AzizSfar/modular_shadow_lamp/output/analytic_projection.png

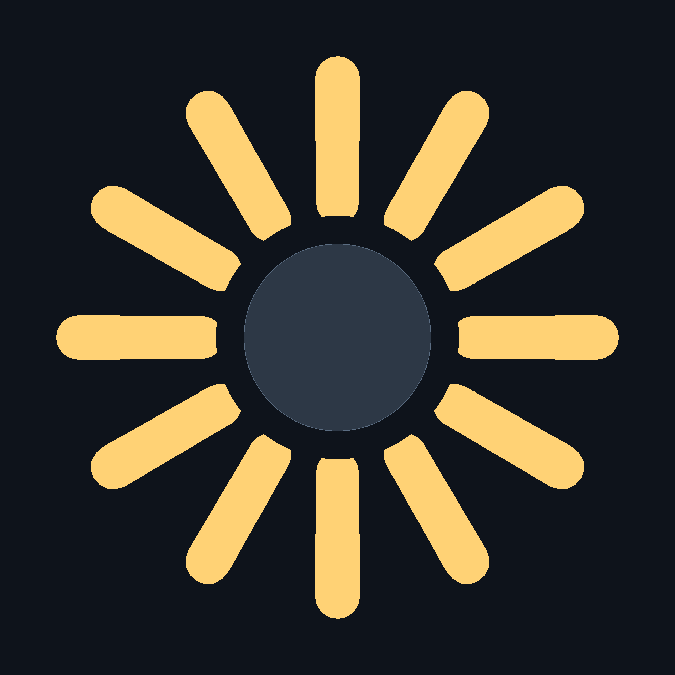
output/analytic_projection.png
