AzizSfar/modular_shadow_lamp/output/demo_projection.png

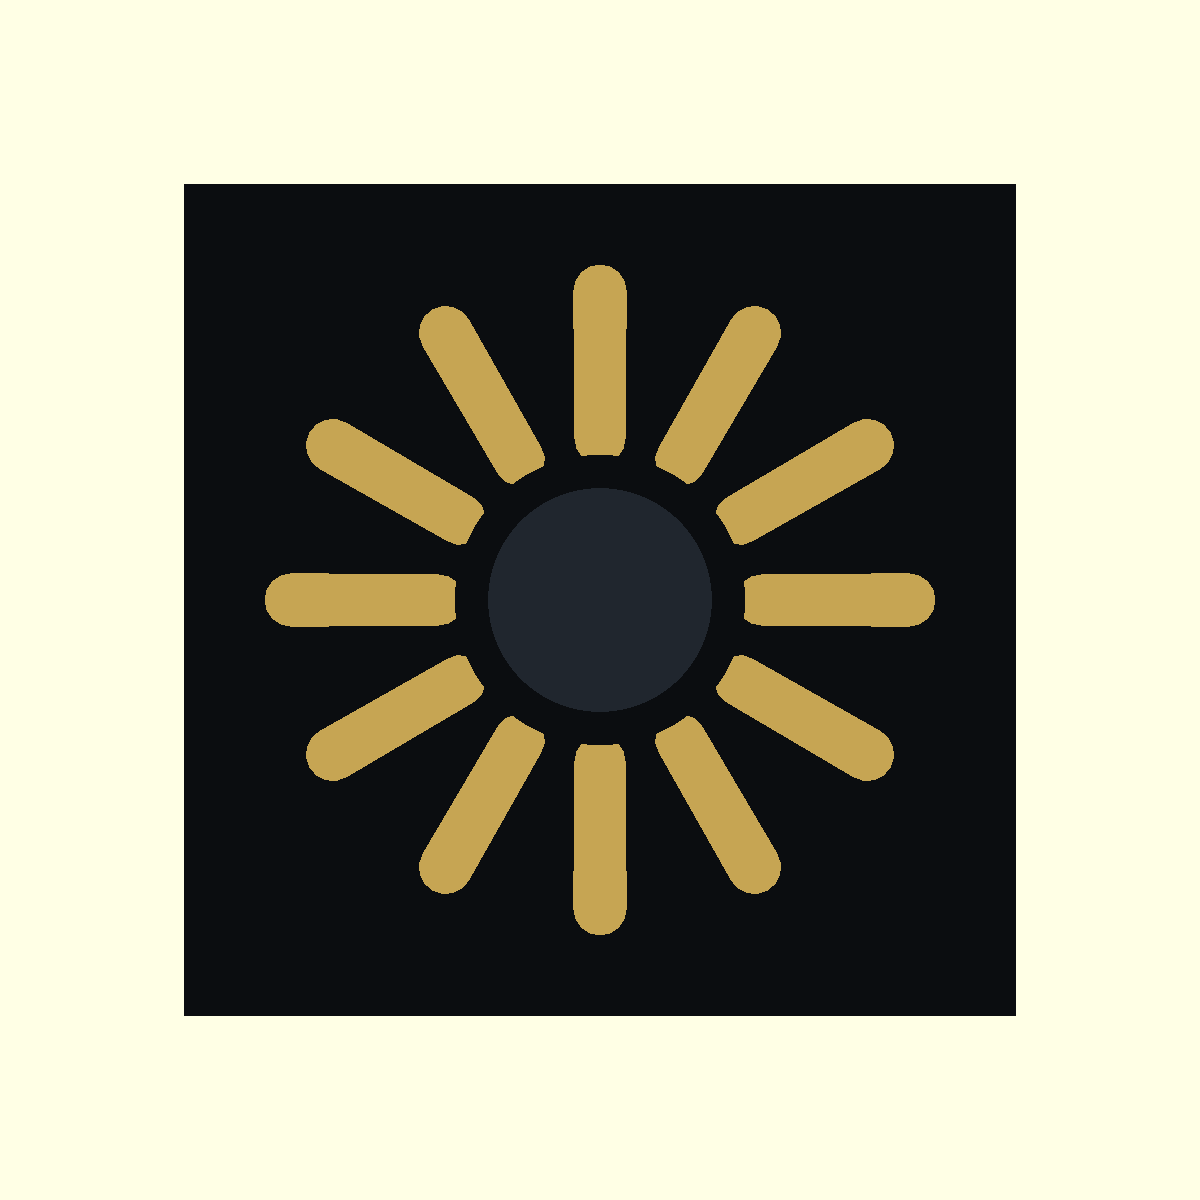
output/demo_projection.png
