AzizSfar/modular_shadow_lamp/output/features_analytic_projection.png

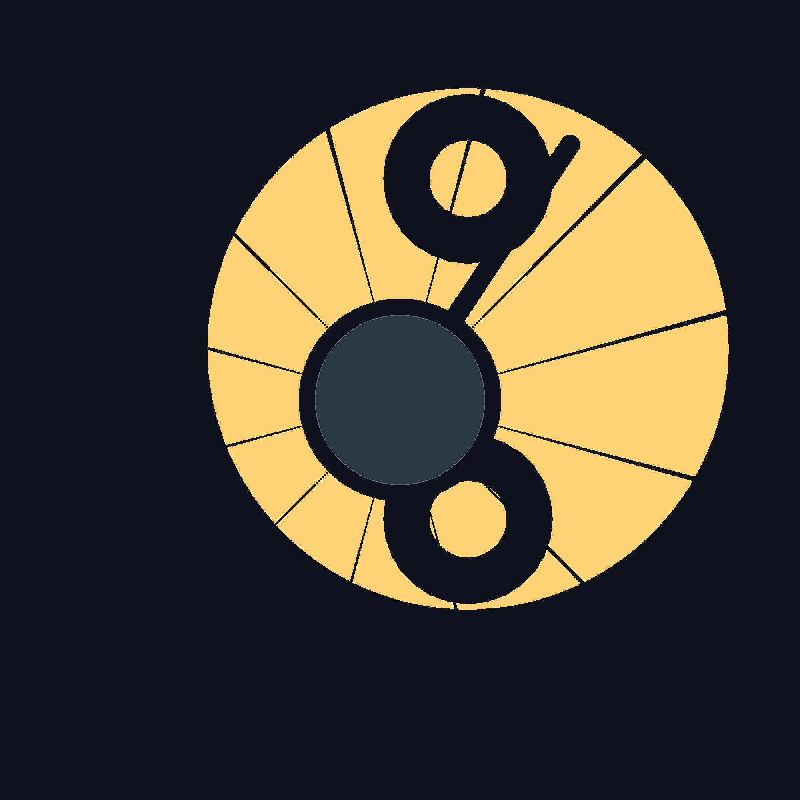
output/features_analytic_projection.png
