AzizSfar/modular_shadow_lamp/output/features_projection.png

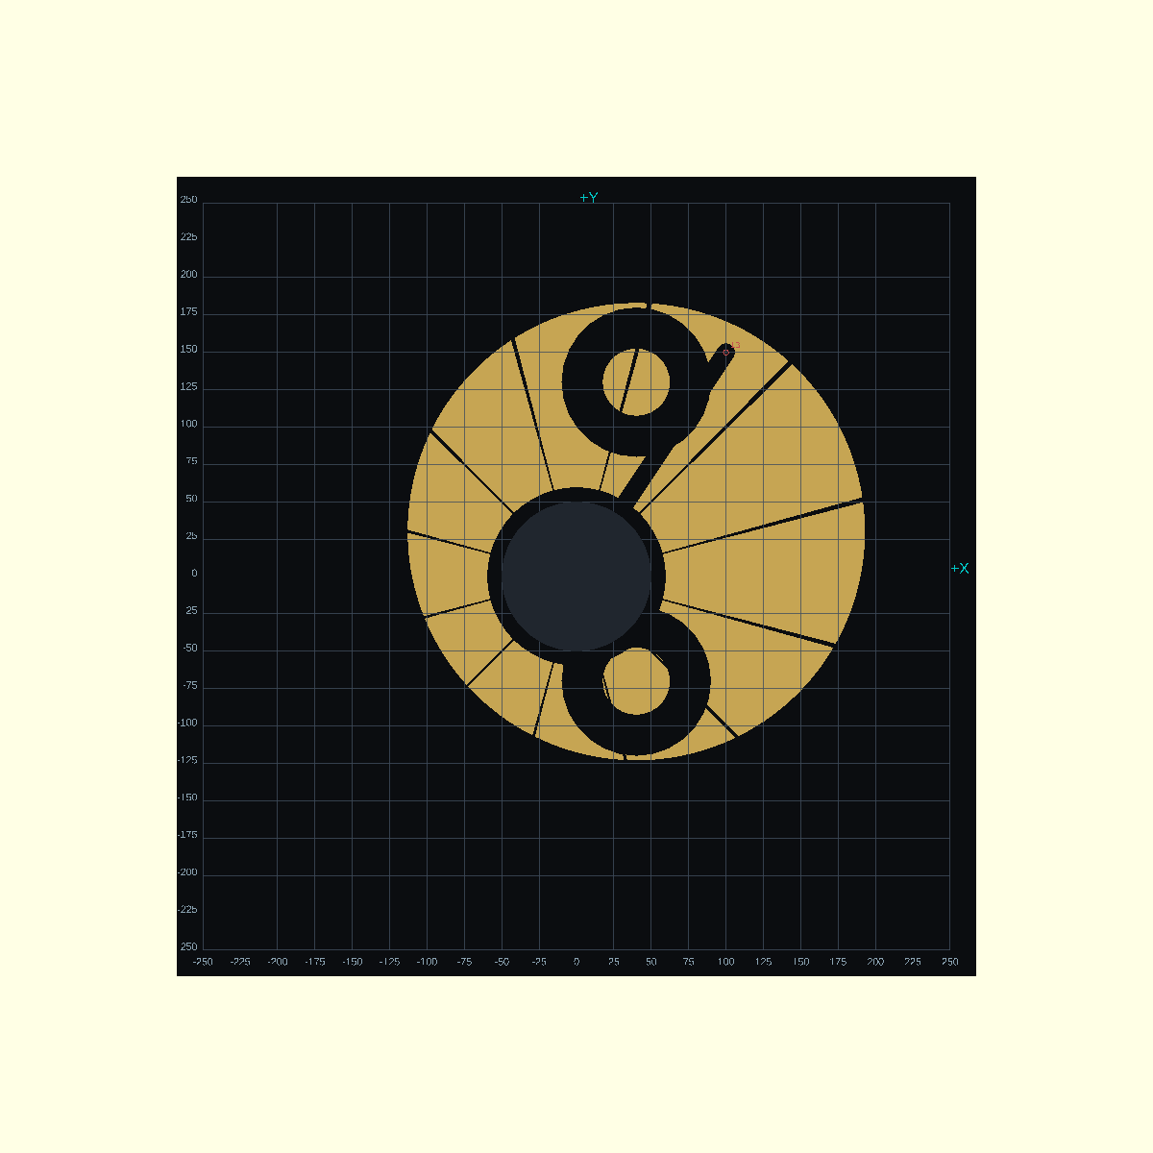
output/features_projection.png
