AzizSfar/modular_shadow_lamp/output/itachi_balanced_projection/comparison.png

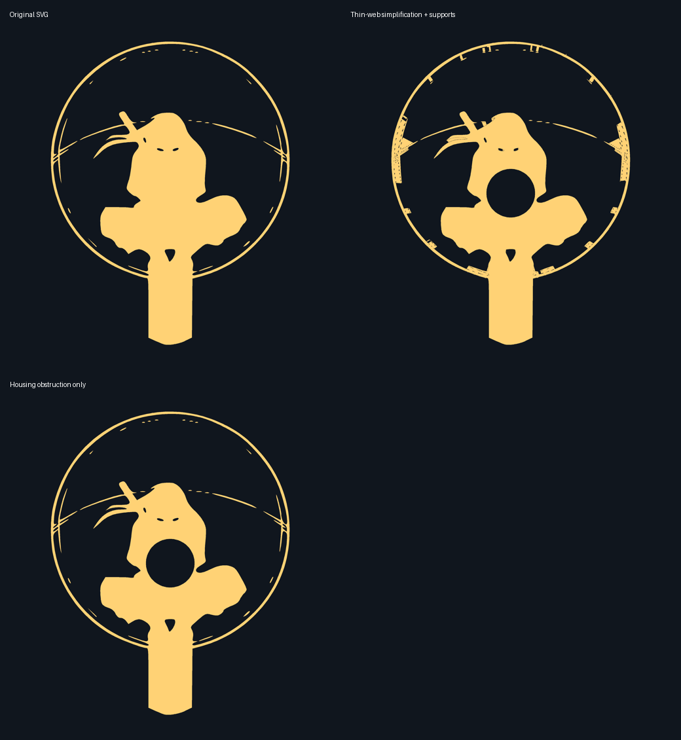
output/itachi_balanced_projection/comparison.png
