AzizSfar/modular_shadow_lamp/output/itachi_balanced_projection/original.png

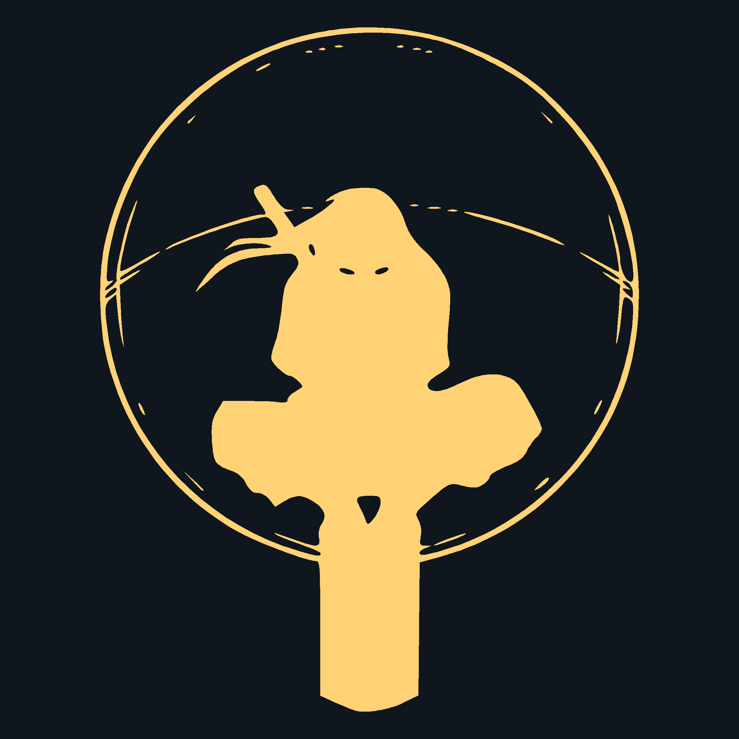
output/itachi_balanced_projection/original.png
