AzizSfar/modular_shadow_lamp/output/itachi_final_projection/comparison.png

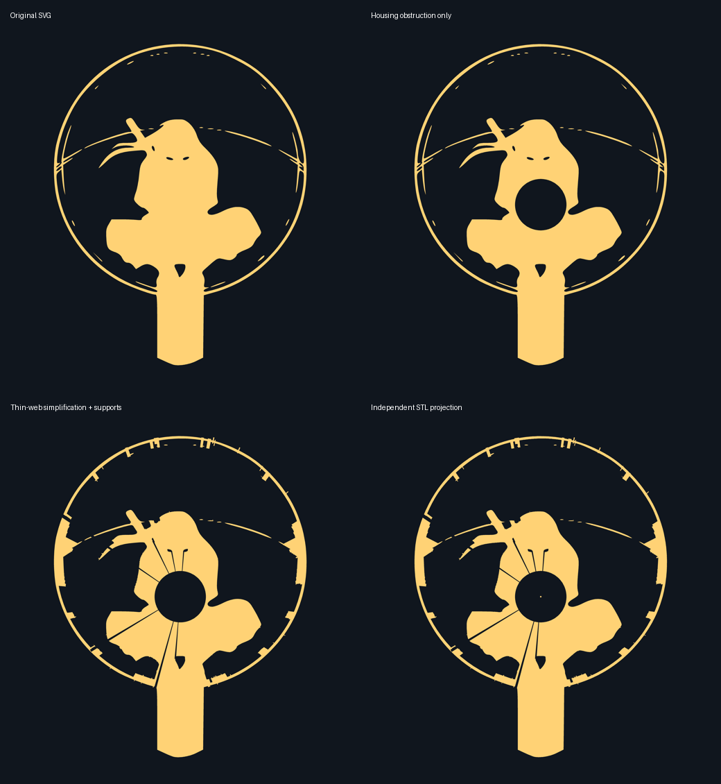
output/itachi_final_projection/comparison.png
