AzizSfar/modular_shadow_lamp/output/itachi_final_projection/mesh.png

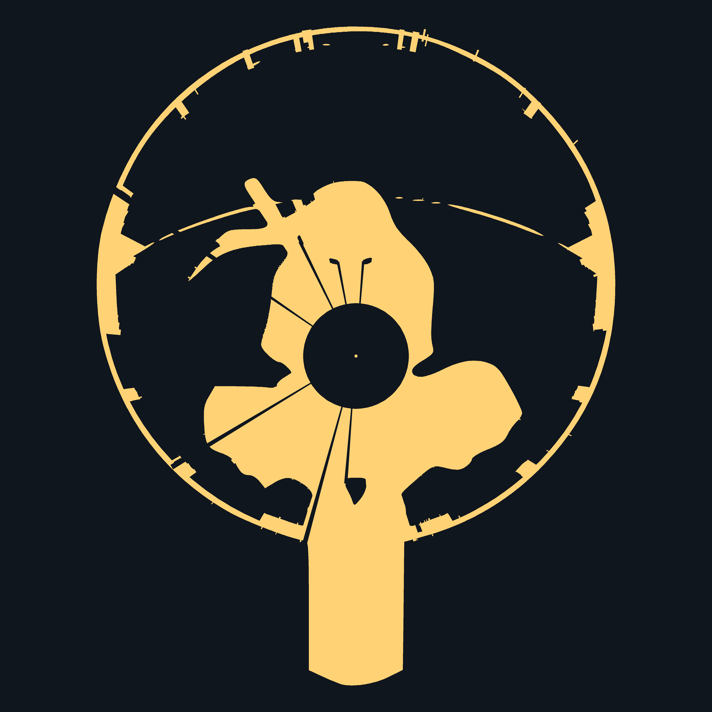
output/itachi_final_projection/mesh.png
