AzizSfar/modular_shadow_lamp/output/itachi_refined_projection/comparison.png

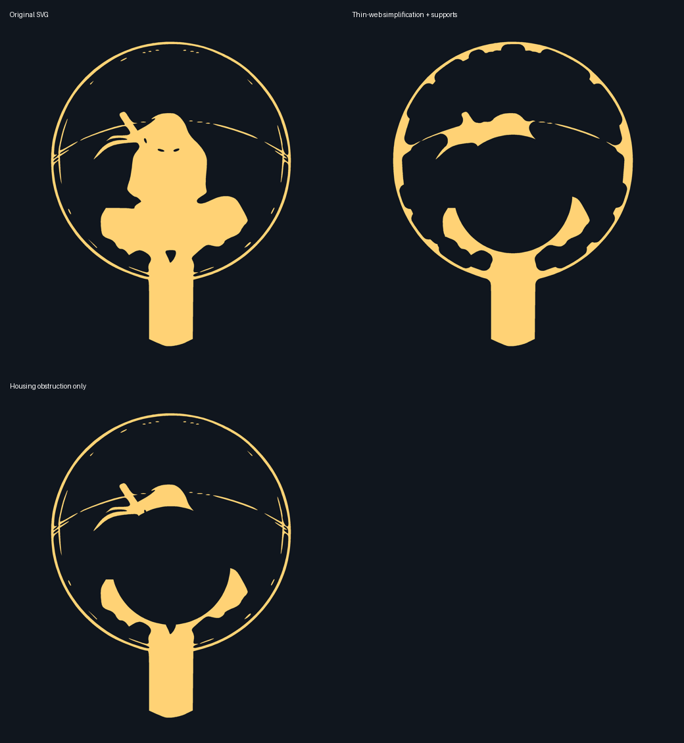
output/itachi_refined_projection/comparison.png
