AzizSfar/modular_shadow_lamp/output/monza_balanced_projection/comparison.png

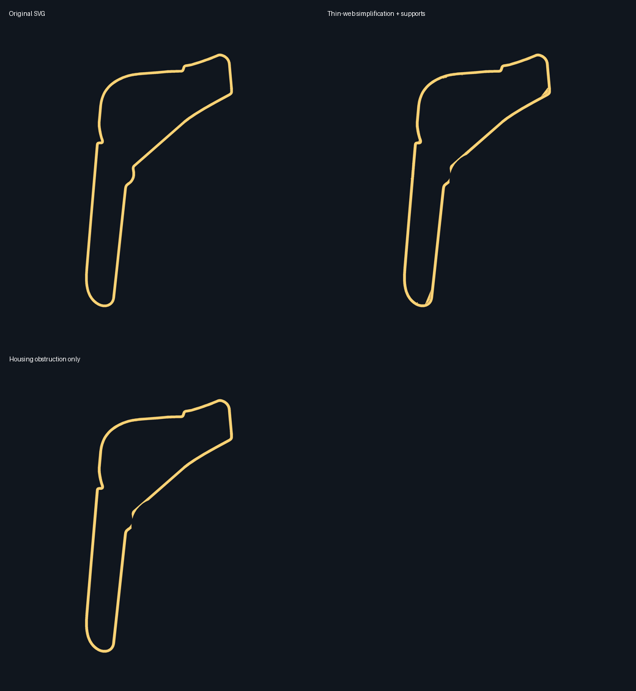
output/monza_balanced_projection/comparison.png
