AzizSfar/modular_shadow_lamp/output/monza_balanced_projection/original.png

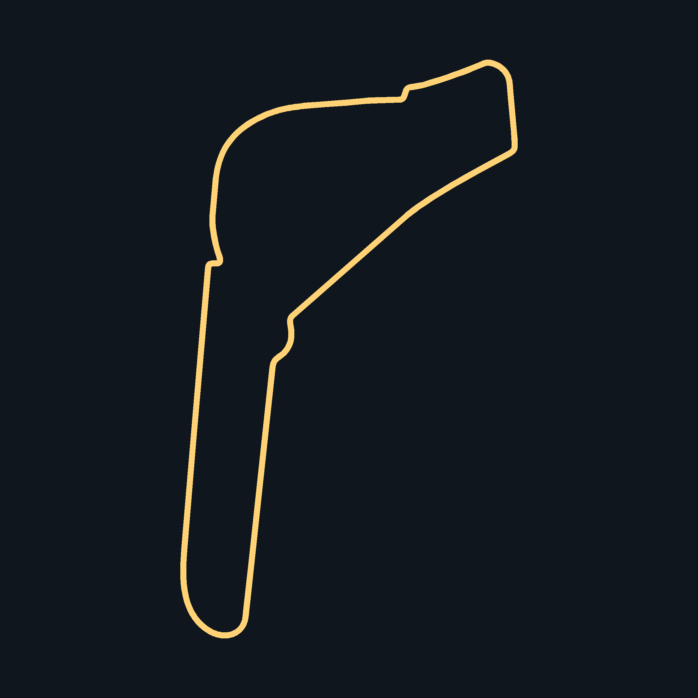
output/monza_balanced_projection/original.png
