AzizSfar/modular_shadow_lamp/output/monza_compact_projection/comparison.png

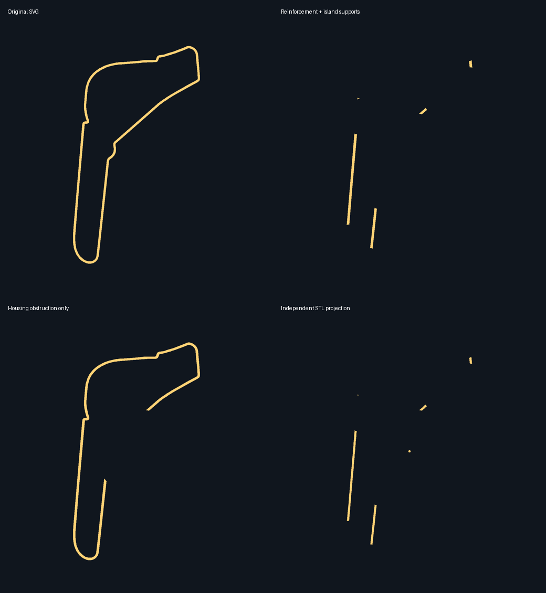
output/monza_compact_projection/comparison.png
