AzizSfar/modular_shadow_lamp/output/monza_compact_projection/mesh.png

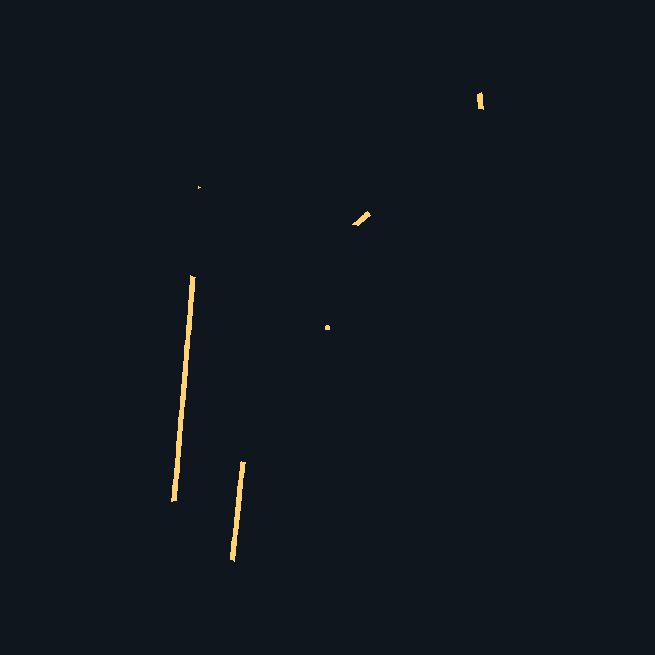
output/monza_compact_projection/mesh.png
