AzizSfar/modular_shadow_lamp/output/monza_final_projection/comparison.png

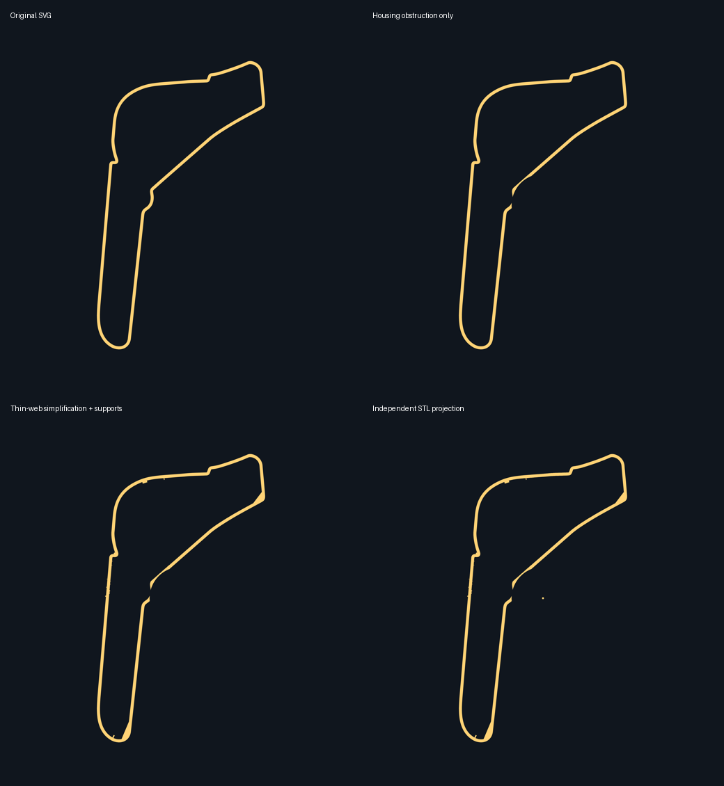
output/monza_final_projection/comparison.png
