AzizSfar/modular_shadow_lamp/output/reference_comparison.png

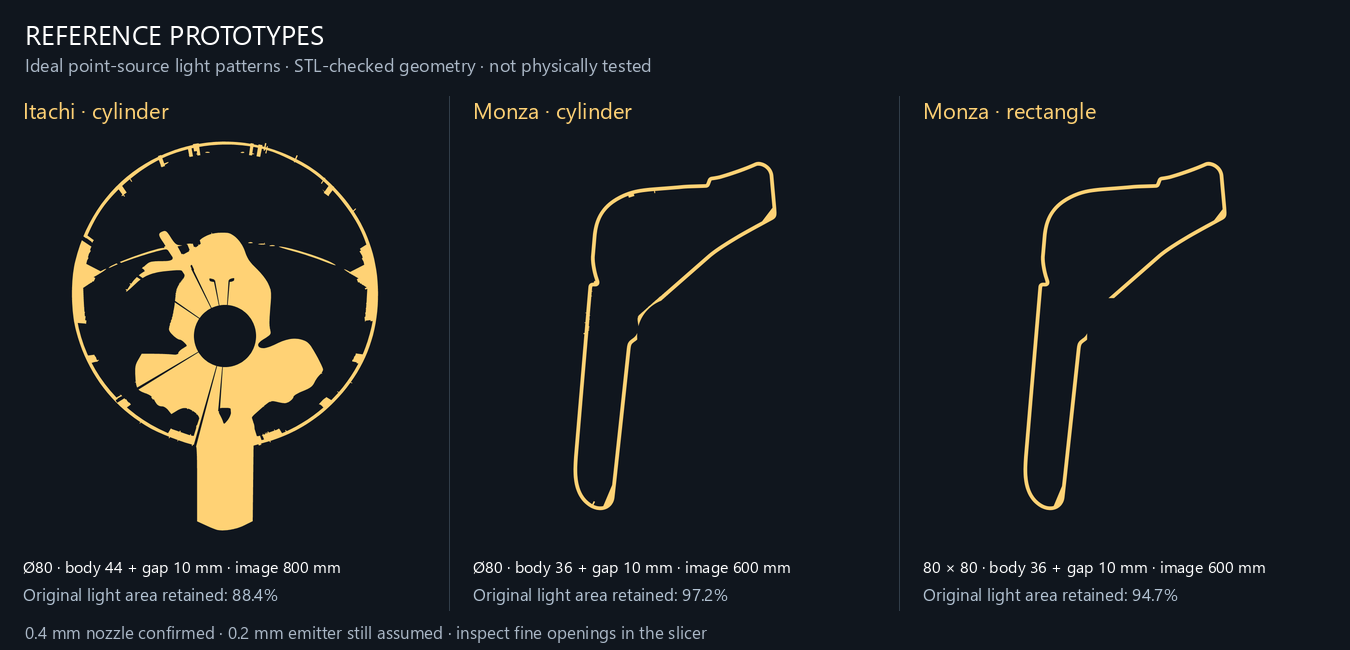
output/reference_comparison.png
