AzizSfar/modular_shadow_lamp/output/reference_study/itachi_example_original.png

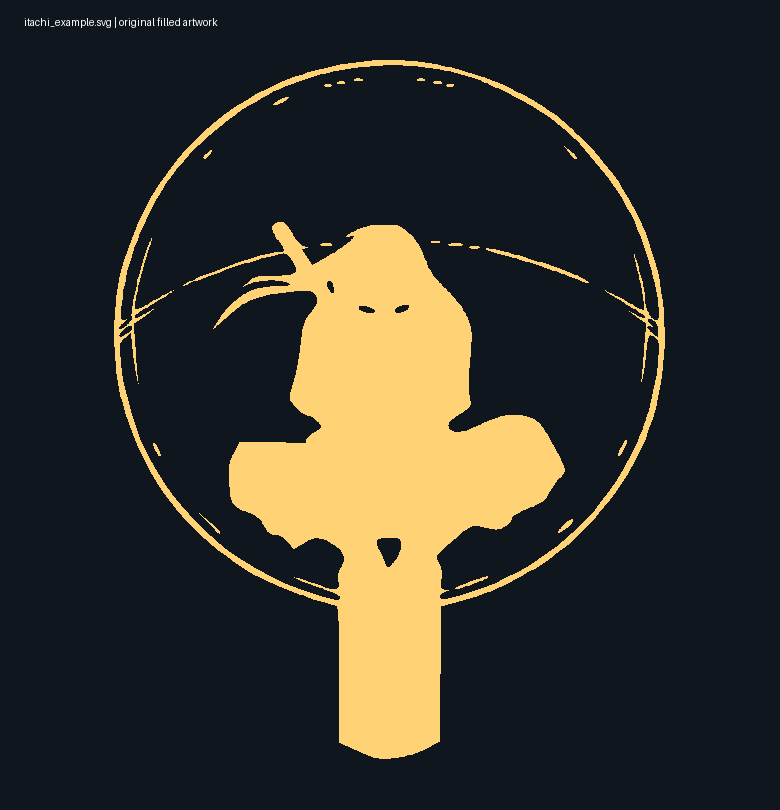
output/reference_study/itachi_example_original.png
