AzizSfar/modular_shadow_lamp/output/two_rings_projection.png

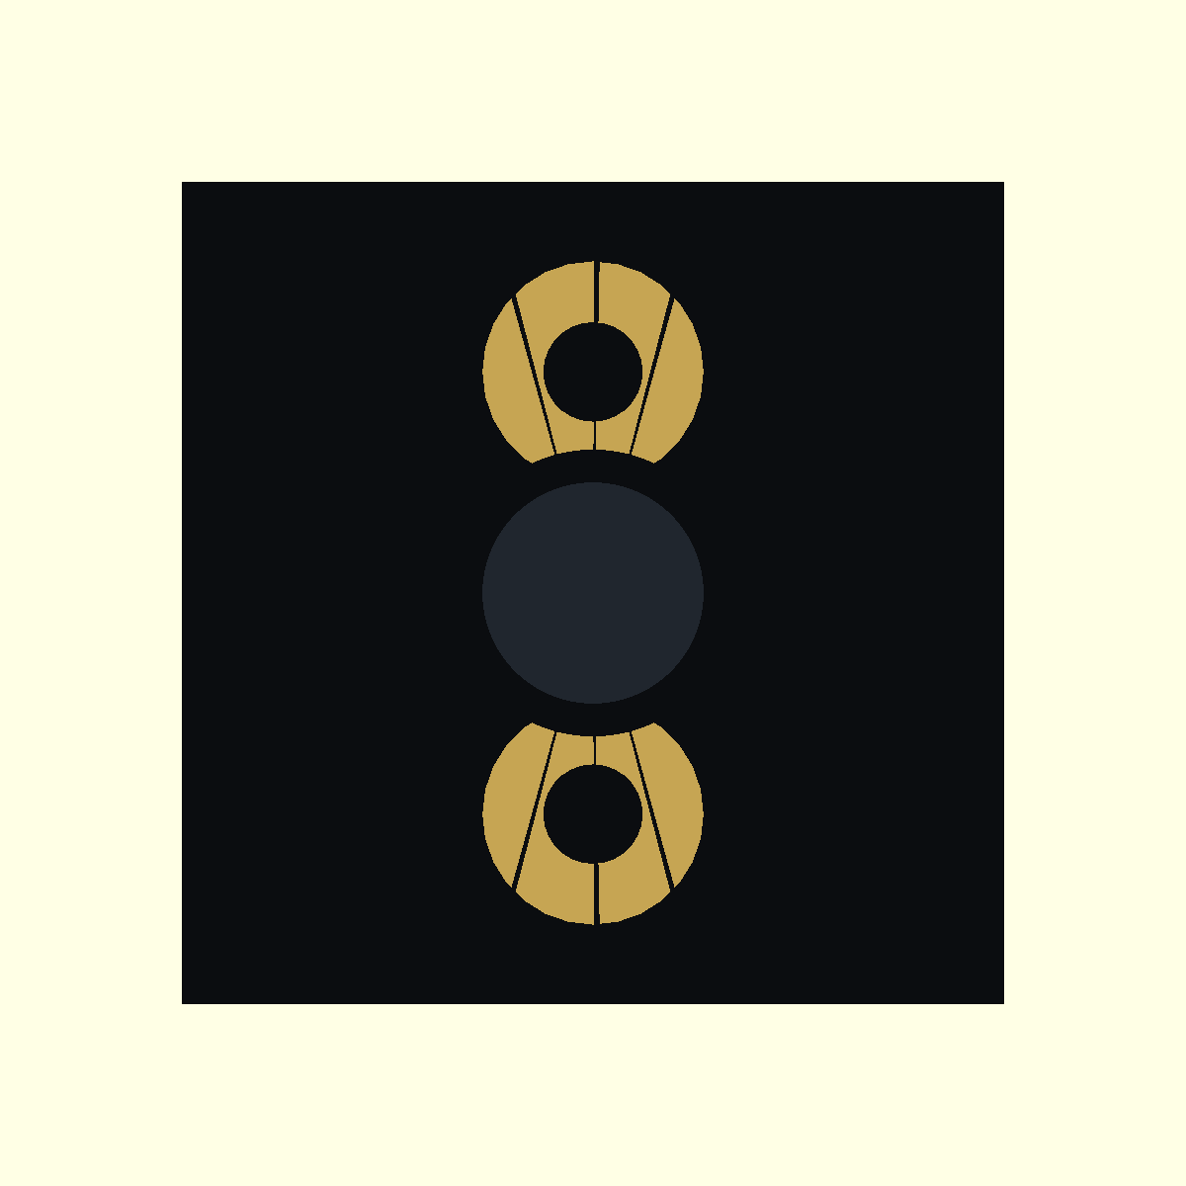
output/two_rings_projection.png
