AzizSfar/modular_shadow_lamp/tools/openscad-2021.01/examples/Basics/projection.stl

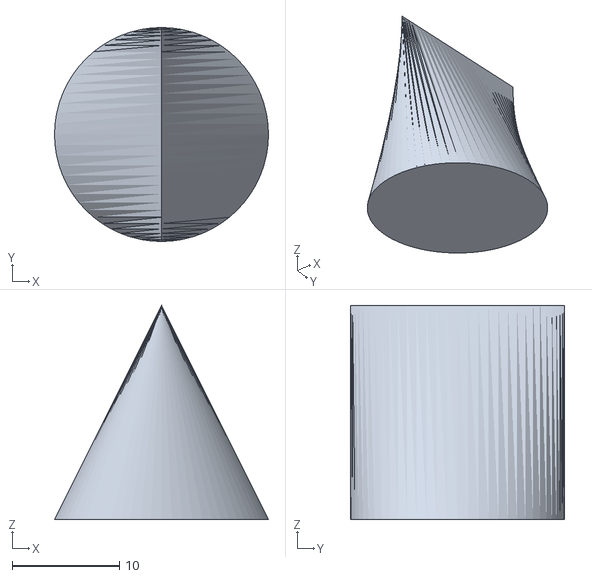
[picture p37: CAD file, 2026-09-13]
tools/openscad-2021.01/examples/Basics/projection.stl
20.0 x 20.0 x 20.0
