AzizSfar/modular_shadow_lamp/output/features_demo_preflight/cover_artwork.stl

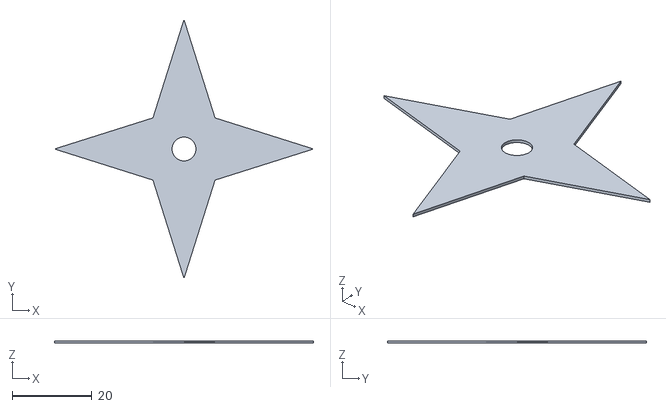
[picture p38: CAD file, 2026-09-13]
output/features_demo_preflight/cover_artwork.stl
65.0 x 65.0 x 0.6
