AzizSfar/modular_shadow_lamp/output/housing_tests/rectangle_ring.stl

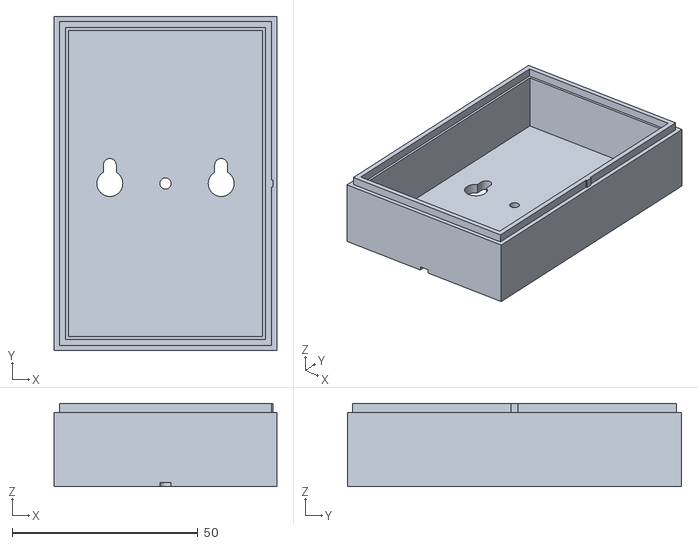
[picture p39: CAD file, 2026-09-13]
output/housing_tests/rectangle_ring.stl
60.0 x 90.0 x 22.5
