AzizSfar/modular_shadow_lamp/output/itachi_compact_standoff.stl

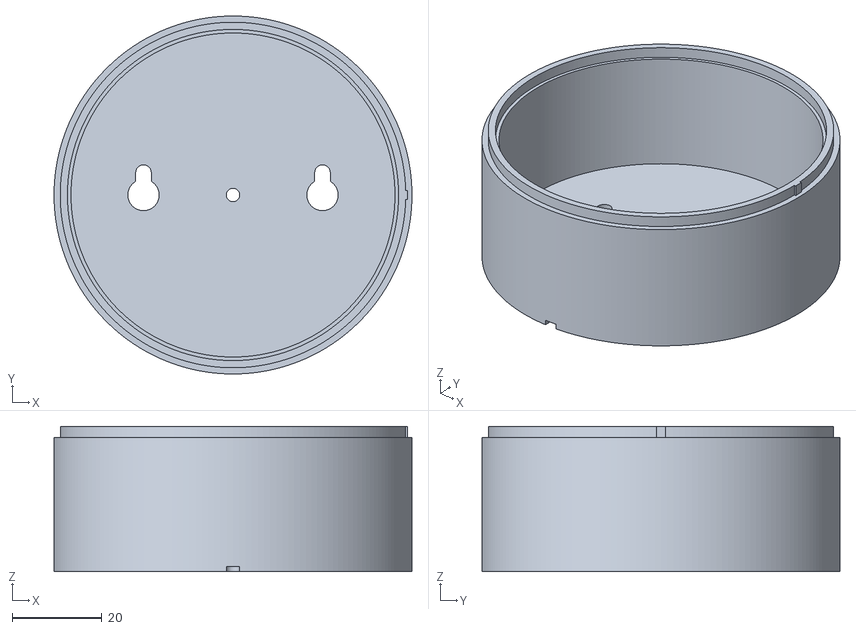
[picture p40: CAD file, 2026-09-13]
output/itachi_compact_standoff.stl
80.0 x 80.0 x 32.5
