AzizSfar/modular_shadow_lamp/output/monza_rectangle_final_preflight/body_0.stl

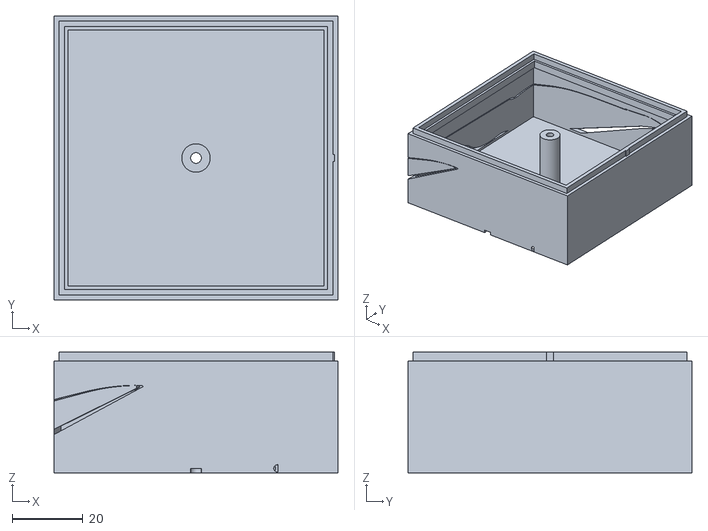
[picture p41: CAD file, 2026-09-13]
output/monza_rectangle_final_preflight/body_0.stl
80.0 x 80.0 x 34.0
