AzizSfar/modular_shadow_lamp/output/standoff_tests/body_ring.stl

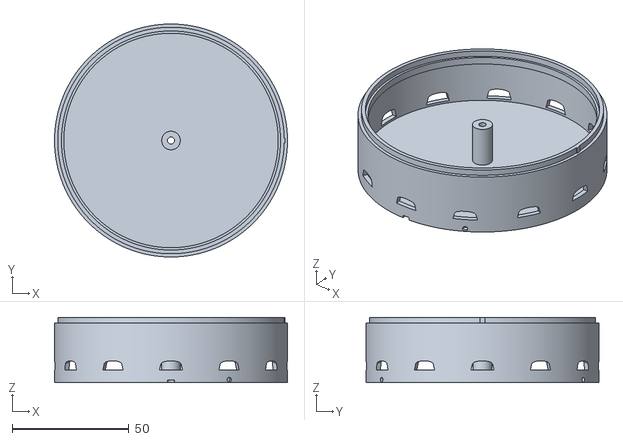
[picture p42: CAD file, 2026-09-13]
output/standoff_tests/body_ring.stl
100.0 x 100.0 x 28.0
