AzizSfar/modular_shadow_lamp/output/features_demo_preflight/body_0.stl

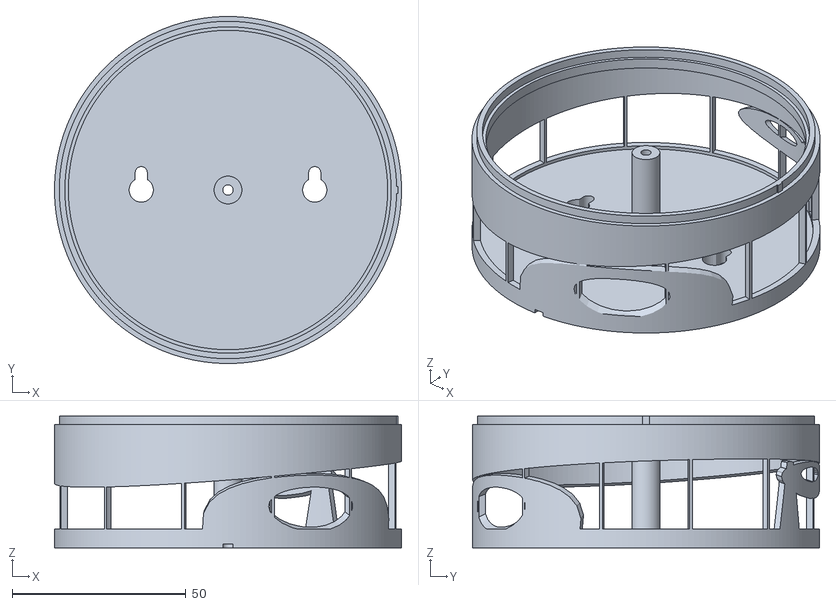
[picture p43: CAD file, 2026-09-13]
output/features_demo_preflight/body_0.stl
100.0 x 100.0 x 38.0
