AzizSfar/modular_shadow_lamp/output/housing_tests/rectangle_body.stl

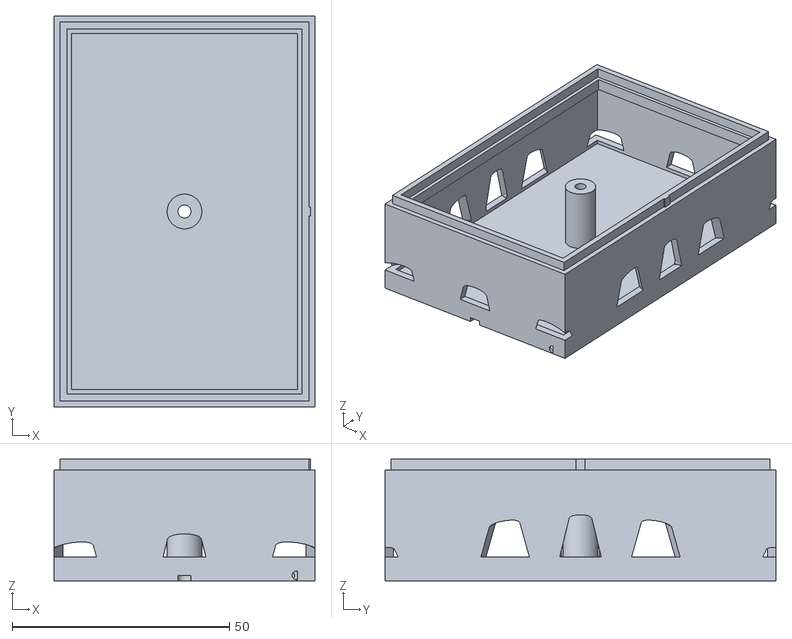
[picture p44: CAD file, 2026-09-13]
output/housing_tests/rectangle_body.stl
60.0 x 90.0 x 28.0
