AzizSfar/modular_shadow_lamp/output/itachi_final_preflight/standoff.stl

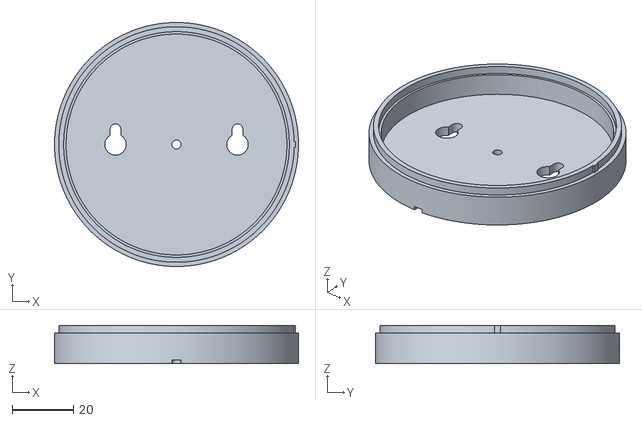
[picture p45: CAD file, 2026-09-13]
output/itachi_final_preflight/standoff.stl
80.0 x 80.0 x 12.5
