AzizSfar/modular_shadow_lamp/output/standoff_tests/ring_hollow.stl

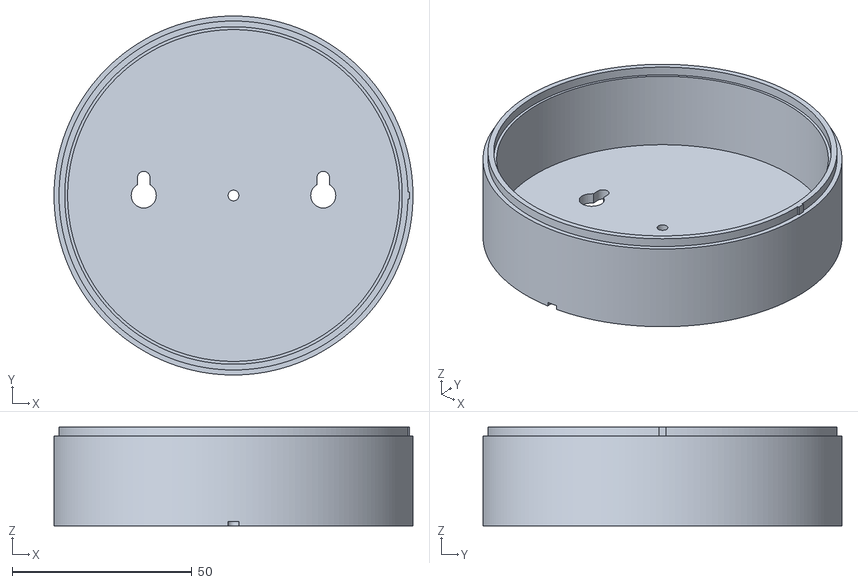
[picture p46: CAD file, 2026-09-13]
output/standoff_tests/ring_hollow.stl
100.0 x 100.0 x 27.5
