AzizSfar/modular_shadow_lamp/output/housing_tests/roundoff.stl

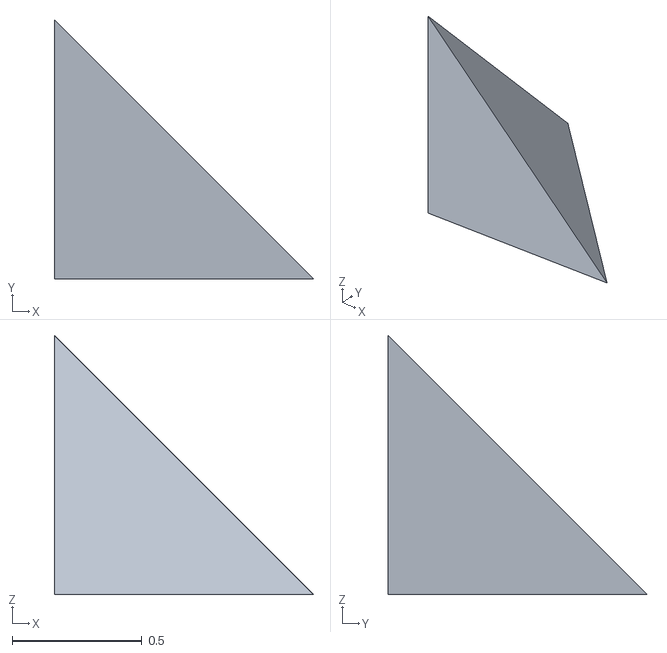
[picture p47: CAD file, 2026-09-13]
output/housing_tests/roundoff.stl
1.00 x 1.00 x 1.00
