AzizSfar/modular_shadow_lamp/output/itachi_final_preflight/body_0.stl

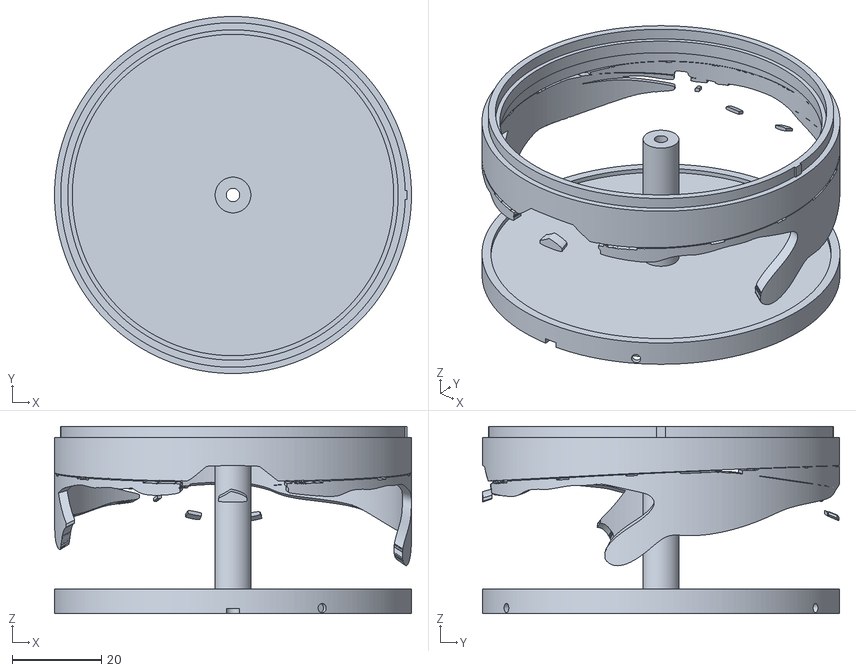
[picture p48: CAD file, 2026-09-13]
output/itachi_final_preflight/body_0.stl
80.0 x 80.0 x 42.0
