AzizSfar/modular_shadow_lamp/output/standoff_tests/ring.stl

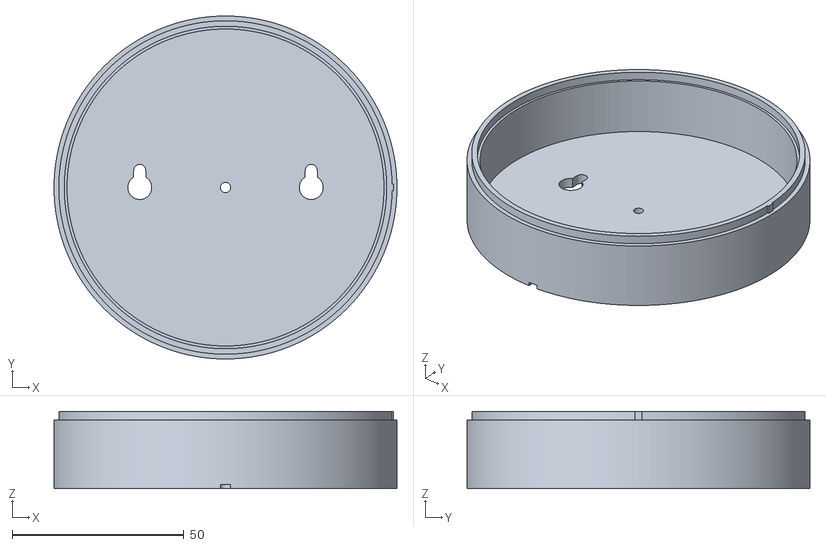
[picture p49: CAD file, 2026-09-13]
output/standoff_tests/ring.stl
100.0 x 100.0 x 22.5
