AzizSfar/modular_shadow_lamp/output/standoff_tests/body_extended.stl

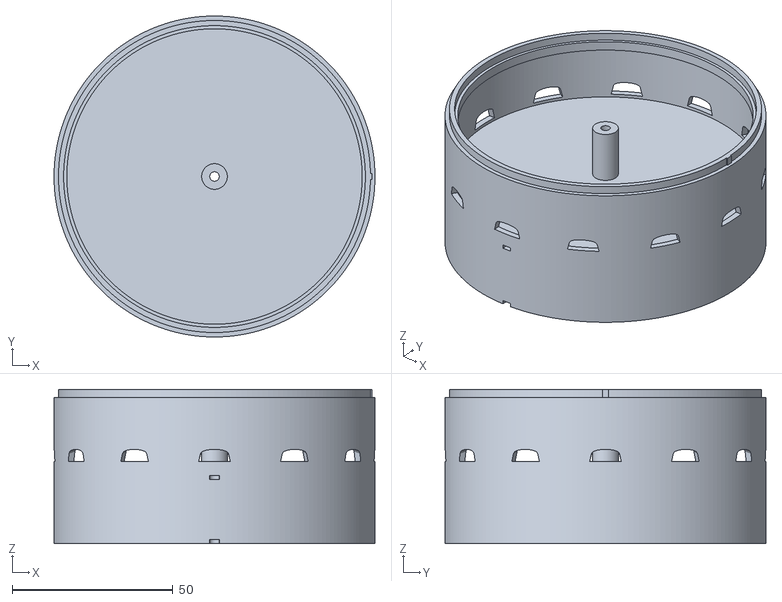
[picture p50: CAD file, 2026-09-13]
output/standoff_tests/body_extended.stl
100.0 x 100.0 x 48.0
