AzizSfar/modular_shadow_lamp/output/standoff_tests/ring_solid.stl

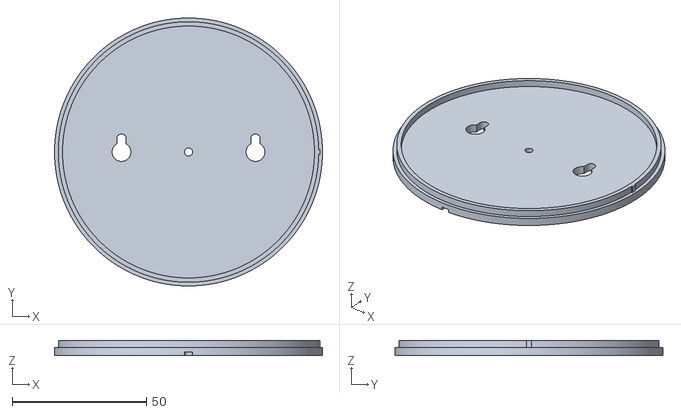
[picture p51: CAD file, 2026-09-13]
output/standoff_tests/ring_solid.stl
100.0 x 100.0 x 5.48
