AzizSfar/modular_shadow_lamp/output/light_cone_debug.stl

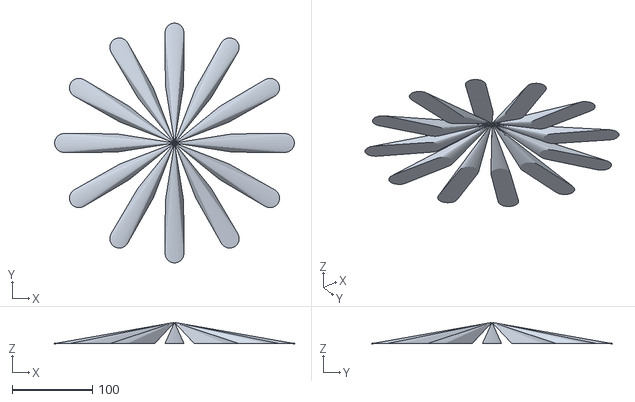
[picture p52: CAD file, 2026-09-13]
output/light_cone_debug.stl
300.0 x 300.0 x 26.4
