AzizSfar/modular_shadow_lamp/output/optical_cutters_debug.stl

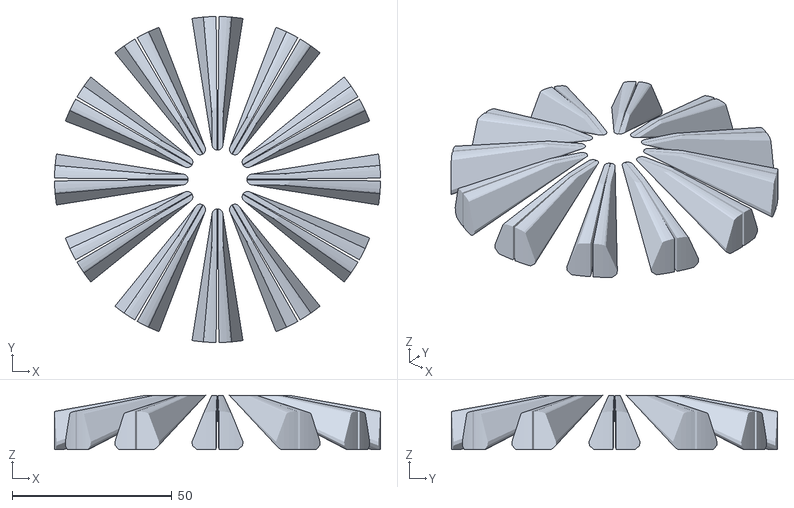
[picture p53: CAD file, 2026-09-13]
output/optical_cutters_debug.stl
102.0 x 102.0 x 17.0
