AzizSfar/modular_shadow_lamp/output/keyhole_debug.stl

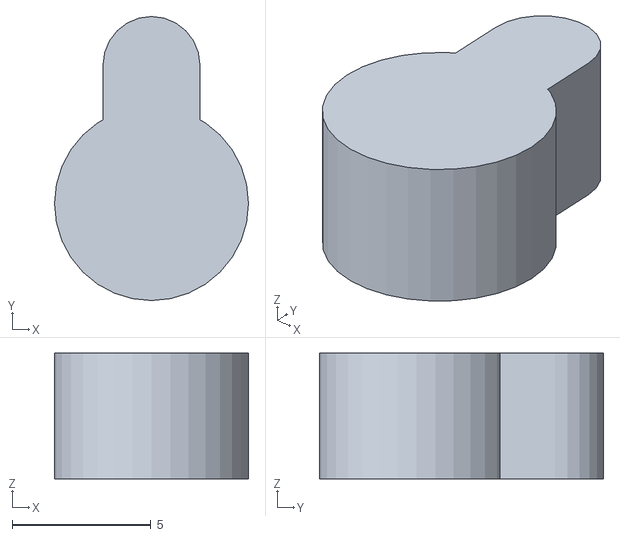
[picture p54: CAD file, 2026-09-13]
output/keyhole_debug.stl
7.00 x 10.2 x 4.54
