AzizSfar/modular_shadow_lamp/output/itachi_balanced.scad

// Artwork is embedded. To replace it, select Artwork_source = SVG file, or rerun prepare_svg.py.
// Modular shadow lamp — millimetres. Read README.md and OPTICS.md.
// Self-contained OpenSCAD 2021.01 / MakerWorld Parametric Model Maker.
// The wall is XY at z=0; +z points into the room. Filled SVG areas transmit light.

/* [View] */
Output = "Assembly"; // [Assembly,Projection,Body,Cover,Cover base,Cover artwork,Standoff,Print layout,Stack preview,Diagnostics]
Show_rays = false;
Show_report = true;
Cover_preview = "Exploded"; // [Exploded,Fitted,Hidden]
// Wall coordinates in mm: cylinder centre = (0,0), X right, Y up.
Show_grid = false;
Grid_spacing = 25; // [5:5:100]

/* [Artwork] */
// Automatic uses a changed file path first, then embedded artwork, then the demo.
// Choose SVG file explicitly if MakerWorld keeps the uploaded filename default.svg.
Artwork_source = "Automatic"; // [Automatic,SVG file,Built-in demo,Embedded artwork]
// MakerWorld recognizes this variable as an SVG upload control.
Svg_file = "default.svg";
// Select the LONGER artwork axis. The other axis scales proportionally.
Svg_long_axis = "Y"; // [X,Y]
// Longest dimension of the complete artwork BEFORE central occlusion, in mm.
Shadow_length = 800.0; // [100:5:1500]
// Light shapes matches luminous outlines in the reference photo.
Artwork_mode = "Light shapes"; // [Light shapes,Dark silhouette]
// Small lit border around the dark silhouette field; avoids tangential, invalid cuts.
Dark_field_border = 3; // [0.5:0.5:20]
Artwork_rotation = 0; // [-180:1:180]
Shadow_x = 0; // [-1000:1:1000]
Shadow_y = 0; // [-1000:1:1000]
// Smallest IMPORTANT line or gap, as % of the artwork's longest dimension.
// This is a declared design requirement, NOT an automatic SVG measurement.
Smallest_detail_percent = 5; // [0.1:0.1:20]

/* [Cylinder] */
Housing_shape = "Cylinder"; // [Cylinder,Rectangle]
Rectangle_width = 80; // [40:1:250]
Rectangle_depth = 100; // [40:1:250]
Cylinder_diameter = 80.0; // [60:1:250]
// Total closed depth of one module, including its fitted cover.
Cylinder_height = 44.0; // [18:0.5:200]
Wall_thickness = 2; // [1.2:0.1:4]
// 0 = first module at wall; 1 = second module, etc. Recompute each module.
Module_index = 0; // [0:1:8]

/* [LED and optical quality] */
LED_position = "Automatic"; // [Automatic,Manual height]
// Height of the EMITTING CENTRE above this module's back, not package bottom.
Manual_LED_height = 24; // [0:0.1:200]
// Width of the actual emitting area, not the plastic lens or LED package.
Emitter_diameter = 0.2; // [0:0.01:5]
// Axial thickness of the emitting area. 0 assumes a planar emitter parallel to wall.
Emitter_axial_depth = 0; // [0:0.01:2]
Maximum_blur = 2; // [0.1:0.1:20]
Minimum_cut_width = 0.4; // [0.15:0.05:2]
// Emitting centre above the end of the printed pillar; measure your LED assembly.
Emitter_above_pillar = 3; // [1:0.1:10]
Pillar_diameter = 8; // [4:0.5:20]
// Continuous empty passage through the rear floor and the whole pillar, in mm.
Pillar_wire_bore = 3; // [1:0.1:6]

/* [Stencil supports] */
// Spokes interrupt light but can connect otherwise floating opaque islands.
// They do NOT guarantee connectivity for arbitrary artwork; run prepare_svg.py.
Support_bridges = true;
Support_layout = "Radial"; // [Radial,Manual XY,Radial and XY]
Bridge_count = 12; // [3:1:48]
Bridge_width = 0.9; // [0.4:0.1:2]
Bridge_rotation = 15; // [0:1:180]
// Helper mode disables the regular spokes and retains only mesh-detected repairs.
Automatic_bridges_only = true;
// Simplify narrow opaque strips in wall space using a conservative shell scale.
// 0 preserves the original geometry. This changes the shadow; inspect Projection.
Minimum_web_width = 0.6; // [0:0.1:2]

/* [Manual XY supports] */
// Segments are specified on the WALL grid. Width is the dark strip width on the wall.
// Enable Manual XY or Radial and XY in Support_layout to use these segments.
Support_1_enabled = true;
Support_1_start = [0,0];
Support_1_end = [0,200];
Support_1_width = 8; // [0.5:0.5:50]
Support_2_enabled = false;
Support_2_start = [0,0];
Support_2_end = [200,0];
Support_2_width = 8; // [0.5:0.5:50]
Support_3_enabled = false;
Support_3_start = [0,0];
Support_3_end = [0,-200];
Support_3_width = 8; // [0.5:0.5:50]
Support_4_enabled = false;
Support_4_start = [0,0];
Support_4_end = [-200,0];
Support_4_width = 8; // [0.5:0.5:50]

/* [Cover artwork and wiring] */
// White FLUSH inlay on the outward-facing circular cover; independent of shadow SVG.
Cover_artwork_source = "Automatic"; // [Automatic,None,SVG file,Embedded artwork]
Cover_svg_file = "default.svg";
Cover_svg_long_axis = "Y"; // [X,Y]
Cover_artwork_length = 65; // [5:1:240]
Cover_artwork_rotation = 0; // [-180:1:180]
Cover_artwork_depth = 0.6; // [0.2:0.1:1.2]
// Centre hole through both cover and inlay. Zero means a closed cover.
Cover_hole_diameter = 0; // [0:0.1:20]

/* [Mounting] */
// Clear gap held between the room wall and this module's back. 0 = flush to the wall.
// The gap is a closed compartment for the electronics. A standoff lifts the source,
// so the reachable image grows -- but the hidden centre widens at a similar rate.
Wall_standoff = 10.0; // [0:0.5:200]
// Separate ring prints the gap as its own part that plugs into the rear socket.
// Extended body grows the body backwards instead, as one piece with no extra joint.
Standoff_mode = "Separate ring"; // [Separate ring,Extended body]
// Back plate of the compartment. It carries the keyholes and the cable route.
Standoff_back = 3; // [1.5:0.1:8]

/* [Joints and cover] */
Joint_depth = 2.5; // [1.5:0.1:4]
Joint_clearance = 0.2; // [0.1:0.05:0.4]
Cover_plate = 2; // [1.5:0.1:3]
// Radial pilot holes in female collars for optional retaining screws.
Retaining_screws = true;
Screw_pilot_diameter = 2.1; // [1.5:0.1:3]

/* [Quality] */
Cylinder_facets = 180; // [72:12:360]

/* [Hidden] */
// Compatibility with older saved presets; Artwork_source overrides this control.
Use_svg = false;
$fn = Cylinder_facets;
eps = 0.02;
// prepare_svg.py replaces this block with normalized, embedded SVG geometry.
Embedded_artwork = true;
Embedded_radius_factor = 0.5000706693625946;
// Extra bridge angles added by the helper after checking the actual exported mesh.
Embedded_bridge_angles = [];
// [angle, local top Z] vertical ribs added only as far as a floating island.
Embedded_bridge_segments = [];
Embedded_removed_islands = [];
Embedded_surface_repair = true;
Embedded_surface_signature = [80.0,80,100,44.0,10.0,0,800.0,0,0,0,0.6,24,3,8,2,2.5,2,"Automatic","Light shapes",3,"Cylinder"];
// BEGIN EMBEDDED PRINT LIGHT
module embedded_print_light() { polygon(points=[[92.527917,12.033107],[92.508825,12.179018],[92.489502,12.324899],[92.774071,12.36282],[92.793453,12.21649],[92.812604,12.07013],[92.409912,12.908112],[92.389439,13.053836],[92.368737,13.199528],[92.347805,13.345186],[92.326643,13.490812],[92.305252,13.636404],[92.283631,13.781962],[92.567567,13.824366],[92.589254,13.67836],[92.610711,13.53232],[92.631938,13.386246],[92.652934,13.24014],[92.6737,13.094],[92.694236,12.947827],[91.58527,17.842349],[91.557017,17.986766],[91.528536,18.131139],[91.499828,18.275466],[91.470891,18.419748],[91.441728,18.563985],[91.412337,18.708175],[91.693592,18.765735],[91.723073,18.621102],[91.752326,18.476422],[91.781351,18.331696],[91.810148,18.186924],[91.838717,18.042107],[91.867057,17.897246],[290.670599,32.220261],[290.619423,32.678638],[290.567523,33.136935],[290.514902,33.595149],[290.461557,34.053279],[290.407491,34.511325],[290.352701,34.969285],[290.29719,35.427158],[290.240957,35.884943],[290.184002,36.342638],[290.126325,36.800244],[290.067926,37.257757],[290.008806,37.715178],[289.948964,38.172505],[289.888402,38.629738],[289.827118,39.086874],[292.640533,39.466299],[292.577927,39.927774],[292.514593,40.38915],[292.450531,40.850426],[292.385742,41.3116],[292.320226,41.772671],[292.253982,42.233639],[292.187012,42.694501],[292.119315,43.155258],[292.050891,43.615906],[291.981741,44.076447],[291.911865,44.536878],[291.841263,44.997198],[291.769934,45.457406],[291.697881,45.917501],[291.625101,46.377482],[291.551596,46.837347],[291.477366,47.297096],[291.402411,47.756727],[291.326732,48.21624],[294.182425,48.688873],[294.105271,49.152769],[294.027386,49.616543],[293.94877,50.080193],[293.869423,50.543718],[293.789345,51.007118],[293.708536,51.470391],[293.626997,51.933536],[293.544727,52.396552],[293.461727,52.859437],[293.377997,53.322191],[293.293538,53.784812],[293.208349,54.2473],[293.12243,54.709653],[293.035783,55.171869],[292.948407,55.633948],[292.860302,56.095889],[292.771469,56.557691],[292.681907,57.019352],[292.591618,57.48087],[295.488102,58.049897],[295.396184,58.51584],[295.303531,58.981638],[295.210143,59.447289],[295.116022,59.912792],[295.021166,60.378147],[294.925576,60.843351],[294.829253,61.308403],[294.732197,61.773303],[294.634408,62.23805],[294.535885,62.702642],[294.43663,63.167078],[294.336643,63.631356],[294.235924,64.095477],[294.134473,64.559438],[294.03229,65.023238],[293.929376,65.486877],[293.825731,65.950352],[293.721355,66.413664],[293.616248,66.876811],[293.510411,67.339791],[293.403844,67.802604],[296.33741,68.48052],[296.22904,68.94779],[296.119934,69.414888],[296.010091,69.881814],[295.899512,70.348566],[295.788197,70.815143],[295.676147,71.281543],[295.56336,71.747767],[295.449839,72.213812],[295.335583,72.679677],[295.220592,73.145362],[295.104867,73.610864],[294.988408,74.076184],[294.871216,74.541319],[294.753289,75.006269],[294.63463,75.471032],[294.515238,75.935608],[297.489655,76.702509],[297.368317,77.171586],[297.24624,77.640471],[297.123423,78.109163],[296.999867,78.57766],[296.875573,79.045962],[296.75054,79.514067],[296.624769,79.981975],[296.49826,80.449684],[296.371014,80.917192],[296.24303,81.3845],[296.11431,81.851604],[295.984853,82.318506],[295.85466,82.785202],[298.873089,83.62981],[301.953742,84.49183],[302.086619,84.015512],[302.218745,83.538986],[302.350118,83.062252],[302.48074,82.585311],[302.61061,82.108164],[302.739727,81.630814],[305.892736,82.480992],[306.022436,81.998465],[306.151376,81.515733],[306.279554,81.032799],[306.40697,80.549664],[306.533624,80.066328],[306.659516,79.582793],[306.784645,79.09906],[306.909011,78.61513],[307.032613,78.131005],[307.155452,77.646686],[307.277527,77.162173],[307.398838,76.677468],[307.519384,76.192573],[307.639165,75.707488],[307.758181,75.222215],[307.876432,74.736755],[307.993916,74.251109],[308.110635,73.765278],[308.226587,73.279264],[308.341773,72.793067],[308.456192,72.30669],[308.569844,71.820132],[308.682728,71.333396],[308.794844,70.846482],[308.906192,70.359393],[309.016772,69.872128],[309.126583,69.38469],[309.235626,68.897078],[309.343899,68.409296],[309.451403,67.921343],[309.558137,67.433222],[306.367347,66.73815],[306.472219,66.254893],[306.576328,65.771472],[306.679676,65.287888],[306.78226,64.804141],[306.884081,64.320233],[306.985139,63.836165],[307.085434,63.351938],[307.184965,62.867553],[307.283731,62.383012],[307.381734,61.898316],[307.478972,61.413466],[307.575445,60.928464],[307.671153,60.443309],[307.766095,59.958005],[307.860273,59.472551],[307.953684,58.986949],[308.04633,58.501201],[308.138209,58.015307],[308.229322,57.529269],[308.319668,57.043088],[308.409248,56.556765],[308.49806,56.070301],[308.586105,55.583697],[308.673383,55.096956],[305.524173,54.534835],[305.6098,54.052923],[305.694667,53.570878],[305.778774,53.088699],[305.86212,52.606388],[305.944705,52.123946],[306.026529,51.641374],[306.107593,51.158674],[306.187895,50.675847],[306.267435,50.192894],[306.346213,49.709816],[306.42423,49.226614],[306.501484,48.74329],[306.577976,48.259845],[306.653706,47.77628],[306.728673,47.292595],[306.802877,46.808793],[306.876317,46.324875],[306.948995,45.840842],[307.020909,45.356694],[307.092059,44.872434],[307.162446,44.388062],[307.232069,43.903579],[307.300927,43.418988],[307.369021,42.934288],[304.264789,42.500679],[304.331439,42.020769],[304.397332,41.540755],[304.462467,41.060637],[304.526845,40.580417],[304.590466,40.100096],[304.653329,39.619675],[304.715435,39.139156],[304.776782,38.658539],[304.837372,38.177826],[304.897203,37.697018],[304.956276,37.216117],[305.014591,36.735123],[305.072146,36.254037],[305.128943,35.772862],[305.184981,35.291597],[305.24026,34.810245],[305.29478,34.328806],[305.348541,33.847282],[305.401542,33.365673],[305.453783,32.883981],[305.505265,32.402208],[305.555986,31.920354],[305.605948,31.438421],[302.550381,31.124087],[302.500919,31.601202],[302.450705,32.078238],[302.399738,32.555195],[302.348019,33.03207],[302.295548,33.508863],[299.303,33.177145],[296.369121,32.851931],[293.492201,32.53303],[276.553849,111.498314],[276.37766,111.93433],[276.200784,112.370067],[276.023222,112.805525],[275.844972,113.240702],[275.666037,113.675597],[275.486416,114.11021],[278.213569,115.239833],[280.995256,116.392046],[281.178469,115.948742],[281.360982,115.50515],[281.542796,115.061271],[281.723909,114.617106],[281.904322,114.172655],[282.084034,113.727921],[282.263044,113.282904],[282.441352,112.837605],[282.618957,112.392025],[282.795859,111.946165],[285.651918,113.076751],[285.829896,112.626107],[286.007164,112.175184],[286.18372,111.723981],[286.359565,111.272501],[286.534697,110.820743],[286.709116,110.368711],[286.882823,109.916403],[287.055816,109.463822],[287.228095,109.010969],[290.158511,110.123143],[290.331826,109.665396],[290.504419,109.207376],[290.676289,108.749085],[290.847436,108.290523],[291.01786,107.831691],[291.18756,107.372592],[291.356535,106.913225],[291.524786,106.453593],[288.580571,105.378479],[288.414019,105.833469],[288.24675,106.288197],[288.078764,106.74266],[287.910062,107.196857],[287.740643,107.650788],[284.863701,106.574454],[284.695267,107.023581],[284.526126,107.472442],[284.356277,107.921035],[284.18572,108.369361],[284.014457,108.817416],[283.842488,109.265201],[283.669812,109.712715],[283.496431,110.159955],[280.689984,109.069437],[280.517621,109.511978],[280.34456,109.954248],[280.170802,110.396243],[279.996347,110.837965],[279.821196,111.27941],[279.645349,111.720579],[279.468806,112.16147],[279.291568,112.602082],[291.45537,97.144929],[291.3018,97.604464],[291.147505,98.063756],[290.992486,98.522803],[290.836743,98.981606],[293.803977,99.991457],[293.961309,99.527973],[294.117909,99.064241],[294.273778,98.600264],[294.428915,98.136041],[284.386199,116.223317],[284.202549,116.671679],[284.018192,117.119751],[283.833129,117.567532],[286.728909,118.767003],[289.684386,119.991201],[289.873264,119.53419],[290.061421,119.076881],[290.248857,118.619276],[290.435571,118.161375],[290.621563,117.703181],[290.806832,117.244695],[290.991377,116.785916],[291.175199,116.326847],[291.358296,115.867489],[291.540669,115.407842],[291.722317,114.947909],[288.746048,113.775164],[288.566254,114.230405],[288.385742,114.685362],[288.204512,115.140034],[288.022566,115.594419],[287.839903,116.048517],[287.656525,116.502326],[287.472431,116.955846],[287.287622,117.409074],[296.953889,90.207848],[296.811253,90.676063],[296.667878,91.144053],[296.523765,91.611816],[296.378915,92.079351],[296.233328,92.546656],[296.087004,93.013732],[295.939943,93.480577],[295.792147,93.947188],[295.643614,94.413567],[298.69098,95.38674],[298.841043,94.915555],[298.990363,94.444134],[299.13894,93.972477],[302.254447,94.951193],[302.104323,95.427761],[301.953448,95.904093],[301.801822,96.380185],[301.649445,96.856038],[301.496318,97.331651],[301.34244,97.807021],[301.187814,98.282147],[301.032438,98.75703],[300.876314,99.231666],[297.775012,98.20883],[297.619756,98.67833],[297.46376,99.147584],[297.307024,99.616592],[297.149548,100.085352],[296.991334,100.553864],[296.83238,101.022125],[296.672689,101.490135],[296.512259,101.957892],[296.351092,102.425396],[296.189188,102.892645],[296.026548,103.359639],[299.109639,104.436121],[299.273974,103.964264],[299.437564,103.492148],[299.60041,103.019775],[299.76251,102.547146],[299.923865,102.074262],[300.084474,101.601124],[300.244336,101.127733],[303.404266,102.192055],[303.565056,101.713428],[303.725092,101.234547],[303.884371,100.755415],[304.042895,100.276033],[304.200663,99.796401],[304.357674,99.316521],[304.513928,98.836393],[304.669424,98.35602],[304.824163,97.875403],[304.978144,97.394541],[305.131366,96.913438],[305.283829,96.432094],[305.435533,95.950509],[305.586477,95.468686],[305.736661,94.986626],[302.552439,93.997348],[302.700306,93.520075],[302.847421,93.042568],[306.034747,94.021798],[306.182649,93.539032],[306.329789,93.056034],[306.476167,92.572804],[306.621783,92.089344],[306.766636,91.605655],[306.910726,91.121738],[307.054053,90.637595],[307.196616,90.153226],[307.338415,89.668633],[307.479449,89.183817],[307.619719,88.698779],[307.759224,88.21352],[307.897963,87.728042],[308.035936,87.242346],[308.173143,86.756432],[308.309584,86.270303],[308.445258,85.78396],[308.580164,85.297403],[308.714304,84.810634],[308.847675,84.323654],[305.631052,83.44543],[305.49907,83.927338],[305.366328,84.409037],[305.232826,84.890527],[305.098565,85.371805],[304.963546,85.852871],[304.827768,86.333724],[304.691231,86.814362],[304.553937,87.294783],[301.414728,86.394987],[301.278099,86.870242],[301.140721,87.345281],[301.002594,87.820102],[300.863718,88.294706],[300.724094,88.769089],[300.583722,89.243252],[300.442602,89.717193],[300.300735,90.19091],[300.158121,90.664404],[300.014761,91.137672],[298.612173,105.850128],[298.444865,106.320939],[298.276815,106.791485],[298.108023,107.261766],[297.938489,107.73178],[297.768214,108.201526],[297.597199,108.671003],[297.425443,109.14021],[297.252948,109.609145],[297.079713,110.077807],[296.90574,110.546196],[296.731028,111.01431],[296.555577,111.482148],[296.37939,111.949708],[296.202465,112.41699],[296.024803,112.883992],[295.846405,113.350714],[295.667271,113.817153],[295.487402,114.28331],[295.306798,114.749182],[295.125459,115.214769],[294.943387,115.680069],[294.76058,116.145082],[294.577041,116.609806],[294.392769,117.074239],[294.207764,117.538382],[294.022028,118.002232],[293.835561,118.465788],[293.648362,118.92905],[293.460434,119.392016],[293.271775,119.854686],[293.082387,120.317057],[292.89227,120.779128],[292.701425,121.2409],[295.781969,122.516903],[298.928046,123.820051],[302.141769,125.151218],[305.425343,126.511319],[305.624484,126.029474],[305.822866,125.547316],[306.020487,125.064845],[306.217347,124.582064],[306.413445,124.098972],[306.608781,123.615572],[306.803354,123.131864],[306.997164,122.64785],[307.190211,122.163531],[307.382493,121.678908],[307.574011,121.193983],[307.764764,120.708756],[307.954752,120.223229],[308.143973,119.737403],[308.332429,119.251278],[308.520117,118.764858],[308.707038,118.278142],[308.893191,117.791132],[309.078575,117.303828],[309.263191,116.816233],[309.447038,116.328348],[309.630115,115.840173],[306.301336,114.594796],[306.481683,114.111584],[306.661268,113.628089],[306.84009,113.144311],[307.018149,112.660251],[307.195444,112.175912],[307.371975,111.691293],[307.547742,111.206396],[307.722743,110.721223],[307.896979,110.235775],[308.07045,109.750052],[308.243154,109.264056],[308.415091,108.777789],[308.586262,108.291251],[308.756664,107.804444],[308.926299,107.317368],[309.095166,106.830026],[309.263263,106.342418],[309.430592,105.854545],[306.139342,104.728626],[306.304129,104.245682],[306.468154,103.762479],[306.631417,103.279018],[303.404266,102.192055],[303.242721,102.670428],[303.080422,103.148546],[302.917369,103.626407],[302.753563,104.10401],[302.589004,104.581354],[302.423692,105.058439],[302.257628,105.535262],[302.090812,106.011822],[301.923244,106.488119],[301.754926,106.964151],[258.877862,129.956548],[258.672585,130.364663],[258.466664,130.772455],[258.260101,131.179921],[258.052896,131.587061],[260.533789,132.852125],[263.062847,134.141749],[265.641487,135.456657],[268.27118,136.797598],[270.95346,138.165353],[273.689917,139.560735],[276.482212,140.98459],[279.33207,142.437798],[282.241291,143.921276],[285.211747,145.435979],[285.44076,144.98599],[285.669063,144.53564],[285.896656,144.08493],[286.123537,143.633862],[286.349707,143.182437],[286.575164,142.730655],[286.799909,142.278519],[287.02394,141.826029],[287.247258,141.373186],[287.469861,140.919991],[287.691749,140.466446],[287.912921,140.012552],[288.133378,139.558309],[288.353117,139.103719],[288.57214,138.648783],[288.790444,138.193502],[289.008031,137.737878],[289.224898,137.281911],[289.441046,136.825602],[289.656475,136.368953],[289.871183,135.911965],[290.085169,135.454639],[290.298435,134.996976],[287.275001,133.590994],[287.48533,133.137765],[287.694945,132.684206],[287.903844,132.230316],[288.112027,131.776097],[288.319493,131.32155],[288.526242,130.866677],[288.732274,130.411479],[288.937587,129.955956],[289.142182,129.500109],[289.346058,129.043941],[289.549213,128.587452],[289.751649,128.130642],[289.953364,127.673515],[290.154358,127.216069],[290.35463,126.758307],[290.55418,126.30023],[290.753007,125.841839],[290.951111,125.383135],[291.148492,124.924119],[291.345148,124.464792],[291.54108,124.005155],[291.736286,123.54521],[291.930767,123.084958],[295.003201,124.38037],[294.806673,124.845466],[294.609412,125.310251],[294.411419,125.774725],[294.212693,126.238886],[294.013235,126.702733],[293.813046,127.166265],[293.612126,127.629481],[293.410476,128.092379],[293.208096,128.554958],[293.004987,129.017218],[292.801149,129.479157],[292.596583,129.940774],[292.391289,130.402068],[292.185267,130.863037],[291.978519,131.323681],[291.771045,131.783998],[291.562845,132.243987],[291.35392,132.703648],[291.14427,133.162978],[290.933896,133.621977],[294.028407,135.043244],[293.815064,135.506789],[293.60099,135.969998],[293.386186,136.432868],[293.170652,136.895399],[292.95439,137.357589],[292.737398,137.819438],[292.519678,138.280944],[292.301231,138.742106],[292.082057,139.202923],[291.862156,139.663394],[291.641529,140.123517],[291.420177,140.583292],[291.1981,141.042717],[290.975299,141.501791],[290.751774,141.960514],[290.527526,142.418883],[290.302556,142.876898],[290.076863,143.334558],[289.850448,143.791861],[289.623313,144.248806],[289.395458,144.705393],[289.166882,145.16162],[288.937588,145.617486],[288.707574,146.072989],[288.476843,146.528129],[288.245394,146.982905],[291.34427,148.563092],[291.109608,149.022388],[290.874222,149.481313],[290.638113,149.939866],[290.40128,150.398046],[290.163726,150.855852],[289.92545,151.313283],[289.686452,151.770337],[289.446734,152.227014],[289.206297,152.683312],[288.96514,153.139231],[288.723264,153.594768],[288.48067,154.049924],[288.237358,154.504697],[287.99333,154.959085],[287.748585,155.413087],[287.503124,155.866704],[287.256949,156.319932],[287.010059,156.772772],[286.762455,157.225222],[286.514138,157.67728],[286.265108,158.128947],[286.015366,158.58022],[285.764913,159.031099],[285.513749,159.481582],[285.261875,159.931669],[285.009291,160.381358],[284.755999,160.830647],[287.85063,162.5785],[287.593869,163.032268],[287.336392,163.485631],[287.078201,163.938587],[286.819296,164.391136],[286.559677,164.843275],[286.299346,165.295004],[286.038302,165.746323],[285.776547,166.197229],[285.514082,166.647721],[285.250906,167.0978],[284.98702,167.547462],[284.722426,167.996708],[284.457124,168.445536],[284.191114,168.893945],[283.924397,169.341934],[283.656974,169.789502],[283.388846,170.236647],[283.120012,170.683369],[282.850475,171.129667],[282.580234,171.575538],[282.30929,172.020983],[282.037644,172.466001],[281.765296,172.910589],[281.492248,173.354747],[281.218499,173.798474],[280.944051,174.241769],[280.668904,174.68463],[280.39306,175.127057],[280.116517,175.569048],[283.194175,177.498036],[282.91389,177.944442],[282.632901,178.390406],[282.35121,178.835925],[282.068816,179.281],[281.78572,179.725629],[281.501924,180.169811],[281.217427,180.613545],[280.932231,181.056829],[284.053141,183.068211],[287.244171,185.124785],[290.507711,187.22809],[290.802628,186.769696],[291.096822,186.310838],[291.390291,185.851516],[291.683036,185.391732],[291.975055,184.931487],[292.266348,184.470782],[292.556914,184.009619],[292.846753,183.547997],[293.135863,183.085919],[293.424244,182.623385],[293.711895,182.160398],[293.998816,181.696957],[294.285005,181.233064],[294.570463,180.768721],[294.855187,180.303928],[295.139179,179.838686],[295.422436,179.372997],[295.704959,178.906862],[295.986746,178.440282],[292.661654,176.435699],[292.939548,175.973921],[293.216713,175.511706],[293.493148,175.049055],[293.768854,174.585968],[294.043829,174.122447],[294.318072,173.658492],[294.591584,173.194106],[294.864363,172.729289],[295.136408,172.264043],[295.407719,171.798367],[295.678296,171.332265],[295.948137,170.865737],[296.217242,170.398783],[296.48561,169.931406],[296.753241,169.463606],[297.020134,168.995384],[297.286288,168.526742],[297.551702,168.057681],[297.816377,167.588202],[298.08031,167.118307],[298.343502,166.647995],[298.605953,166.177269],[298.86766,165.70613],[299.128624,165.234578],[299.388844,164.762616],[299.64832,164.290243],[299.90705,163.817463],[300.165034,163.344274],[300.422272,162.87068],[300.678762,162.39668],[297.338486,160.592596],[297.591387,160.123462],[297.843549,159.65393],[298.094969,159.184002],[298.345648,158.713677],[298.595585,158.242957],[298.844779,157.771844],[299.09323,157.300339],[299.340937,156.828442],[299.5879,156.356155],[299.834117,155.883479],[300.079589,155.410416],[300.324314,154.936966],[300.568292,154.46313],[300.811523,153.988911],[301.054005,153.514308],[301.295739,153.039324],[301.536723,152.563959],[301.776957,152.088214],[302.016441,151.612091],[302.255173,151.135591],[302.493154,150.658716],[302.730382,150.181465],[302.966858,149.703841],[303.202579,149.225844],[303.437547,148.747477],[303.67176,148.268739],[303.905218,147.789633],[304.137919,147.310159],[304.369864,146.830319],[304.601053,146.350113],[304.831483,145.869543],[301.48228,144.266865],[301.709429,143.791217],[301.935828,143.315211],[302.161475,142.838849],[302.386371,142.362131],[302.610515,141.885059],[302.833906,141.407634],[303.056544,140.929858],[303.278428,140.451731],[303.499558,139.973255],[303.719933,139.49443],[303.939553,139.015259],[304.158416,138.535742],[304.376523,138.05588],[304.593873,137.575675],[304.810466,137.095127],[305.0263,136.614239],[305.241375,136.133011],[305.455692,135.651444],[305.669248,135.16954],[305.882044,134.6873],[306.09408,134.204724],[306.305354,133.721815],[306.515866,133.238573],[306.725616,132.755],[306.934603,132.271097],[307.142827,131.786865],[307.350287,131.302305],[307.556982,130.817418],[307.762912,130.332206],[307.968077,129.84667],[308.172475,129.36081],[304.823362,127.954961],[305.024781,127.474064],[305.225441,126.992849],[305.425343,126.511319],[302.141769,125.151218],[298.928046,123.820051],[295.781969,122.516903],[292.701425,121.2409],[292.509851,121.70237],[289.494787,120.447915],[289.684386,119.991201],[286.728909,118.767003],[283.833129,117.567532],[283.64736,118.01502],[283.460885,118.462214],[283.273706,118.909114],[283.085821,119.355719],[280.255419,118.162354],[280.068717,118.604199],[279.881317,119.045749],[279.693222,119.487003],[279.50443,119.92796],[279.314944,120.368618],[279.124763,120.808977],[278.933887,121.249036],[278.742318,121.688793],[275.982934,120.484145],[275.792574,120.919249],[275.601529,121.354053],[275.409798,121.788554],[275.217383,122.222753],[275.024282,122.656647],[274.830498,123.090236],[274.63603,123.52352],[274.440879,123.956496],[271.750708,122.741428],[271.556794,123.169854],[271.362204,123.597975],[271.16694,124.025787],[270.971001,124.453292],[270.774388,124.880486],[270.577102,125.30737],[270.379143,125.733943],[270.180511,126.160203],[269.981207,126.586148],[267.360441,125.357349],[267.162407,125.778848],[266.963708,126.200035],[266.764346,126.620908],[266.56432,127.041465],[266.36363,127.461707],[266.162279,127.881632],[265.960265,128.301238],[265.75759,128.720526],[265.554254,129.139493],[263.001244,127.89796],[262.799208,128.312581],[262.596519,128.726883],[262.393177,129.140865],[262.189182,129.554526],[261.984535,129.967864],[261.779236,130.380879],[261.573286,130.79357],[261.366686,131.205936],[275.486416,114.11021],[275.30611,114.544539],[275.125119,114.978582],[274.943443,115.41234],[274.761084,115.845811],[274.578041,116.278994],[274.394316,116.711888],[274.209908,117.144491],[274.024818,117.576803],[276.737502,118.740744],[276.924424,118.304152],[277.110657,117.867266],[277.296202,117.430087],[277.481056,116.992616],[277.665221,116.554854],[277.848695,116.116803],[278.031477,115.678462],[278.213569,115.239833],[262.756748,255.401545],[262.353626,255.815622],[265.552431,258.934711],[265.960468,258.515585],[93.367211,93.662176],[93.21938,93.809309],[93.626423,94.218928],[93.774899,94.071152],[92.986613,95.664496],[92.835625,95.811027],[93.244563,96.233072],[93.396217,96.085896],[80.440524,189.118889],[80.142164,189.245517],[80.687289,190.53276],[80.987678,190.405271],[214.478294,291.706744],[214.017975,292.044636],[213.557124,292.381802],[213.095742,292.71824],[212.63383,293.05395],[212.171389,293.388931],[211.70842,293.723183],[211.244925,294.056704],[210.780904,294.389493],[210.316359,294.721551],[209.851291,295.052875],[209.385701,295.383465],[208.91959,295.713321],[208.452959,296.042441],[207.98581,296.370825],[207.518144,296.698472],[207.049962,297.02538],[206.581264,297.35155],[206.112053,297.676981],[208.594848,301.262754],[211.138188,304.935967],[213.744313,308.699859],[214.230899,308.362378],[214.716952,308.02413],[215.202471,307.685116],[215.687455,307.345337],[216.171902,307.004793],[216.655812,306.663486],[217.139183,306.321416],[217.622014,305.978584],[218.104303,305.63499],[218.58605,305.290637],[219.067253,304.945525],[219.547912,304.599653],[220.028024,304.253025],[220.507589,303.905639],[220.986606,303.557498],[221.465072,303.208601],[218.76481,299.511663],[219.236899,299.166275],[219.708443,298.820144],[217.061867,295.220601],[200.910039,317.202444],[200.409528,317.518906],[202.914142,321.487092],[203.420908,321.166675],[8.135718,111.947574],[7.959155,111.960266],[7.782572,111.972679],[7.60597,111.984814],[7.429349,111.99667],[7.252709,112.008247],[7.076051,112.019546],[7.102257,112.434409],[6.924928,112.44547],[6.95067,112.863458],[6.772664,112.874279],[6.594641,112.88482],[6.619246,113.306007],[6.440542,113.316305],[6.464663,113.740685],[6.488965,114.168256],[6.51345,114.599053],[6.694176,114.588638],[6.874886,114.577938],[6.900926,115.011919],[7.082303,115.000893],[7.263663,114.98958],[7.291279,115.426776],[7.47331,115.415133],[7.501833,115.855622],[7.68454,115.843647],[7.867228,115.831383],[7.897368,116.275154],[8.080737,116.262555],[8.264085,116.249666],[8.447412,116.236488],[8.415172,115.792865],[8.383177,115.352615],[8.351425,114.9157],[8.319912,114.482082],[8.288636,114.051724],[8.257594,113.62459],[8.226784,113.200643],[8.196203,112.779848],[8.165849,112.36217],[19.318229,114.47973],[19.137659,114.510055],[18.957041,114.540094],[18.776375,114.569849],[18.848311,115.008787],[18.9208,115.451101],[18.993849,115.896831],[19.067464,116.346015],[19.141652,116.798695],[19.216419,117.254911],[19.291773,117.714705],[19.36772,118.178119],[19.444267,118.645197],[19.521422,119.115981],[19.333539,119.14662],[19.145609,119.176963],[18.95763,119.207009],[18.769605,119.236759],[18.581533,119.266213],[18.655558,119.741346],[18.844379,119.711776],[19.033154,119.681907],[19.221881,119.651741],[19.41056,119.621277],[19.599192,119.590516],[19.787774,119.559457],[19.976307,119.528101],[20.16479,119.496448],[20.353224,119.464497],[20.541606,119.43225],[20.729938,119.399705],[20.918218,119.366863],[20.835214,118.893215],[21.022695,118.860208],[21.210124,118.826905],[21.3975,118.793307],[21.584823,118.759413],[21.772092,118.725224],[21.959307,118.69074],[21.872517,118.221636],[22.058938,118.186994],[21.972097,117.72172],[21.885937,117.260096],[21.700979,117.294466],[21.616214,116.836314],[21.53211,116.381726],[21.348537,116.41554],[21.164911,116.449064],[21.082882,115.997739],[20.899915,116.030845],[20.716896,116.063662],[20.636913,115.615567],[20.45455,115.64797],[20.375883,115.203198],[20.194171,115.23519],[20.012408,115.266895],[19.935736,114.825286],[19.75462,114.856584],[19.573455,114.887596],[19.392241,114.918323],[72.696513,373.153208],[72.107921,373.267394],[71.519149,373.380651],[70.9302,373.49298],[70.341075,373.60438],[69.751774,373.71485],[69.1623,373.824391],[68.572654,373.933003],[67.982838,374.040684],[67.392852,374.147435],[66.802699,374.253255],[66.21238,374.358144],[67.05034,379.095888],[67.909782,383.955087],[68.791542,388.940472],[69.404856,388.831497],[70.017998,388.721555],[70.630965,388.610645],[71.243757,388.49877],[71.856371,388.385928],[72.468807,388.27212],[73.081062,388.157346],[73.693136,388.041607],[74.305026,387.924903],[74.916732,387.807233],[75.528251,387.6886],[74.56014,382.719261],[73.616534,377.875702],[55.559893,376.086689],[54.966696,376.173845],[54.373363,376.260065],[53.779894,376.34535],[53.186291,376.429698],[52.592556,376.513111],[51.99869,376.595586],[51.404695,376.677125],[50.810572,376.757727],[51.453613,381.525839],[52.113138,386.416185],[52.78979,391.433526],[53.407056,391.349784],[54.024189,391.265069],[54.641188,391.17938],[55.25805,391.092719],[55.874775,391.005085],[56.491362,390.916478],[57.107807,390.826899],[57.724111,390.736348],[56.984211,385.727944],[56.263039,380.846308],[145.227886,361.859238],[144.657016,362.087827],[144.085786,362.315516],[145.956638,367.019927],[146.535285,366.789282],[147.113568,366.557724],[85.393231,380.448739],[84.793117,380.58294],[85.894096,385.52454],[86.502001,385.388597],[82.242229,386.320052],[81.63286,386.449276],[81.023288,386.577539],[82.089158,391.663007],[82.706749,391.533056],[83.324134,391.402132],[-19.342888,111.410613],[-19.51857,111.379968],[-19.694203,111.349047],[-19.767685,111.764503],[-19.943924,111.733189],[-19.869788,111.317849],[-20.045323,111.286373],[-20.220808,111.254622],[-20.396243,111.222593],[-20.571627,111.190288],[-20.74696,111.157706],[-20.922242,111.124847],[-21.000305,111.539467],[-21.078953,111.957193],[-21.158193,112.378059],[-21.23803,112.802101],[-21.318472,113.229356],[-21.399526,113.659859],[-21.481199,114.093649],[-21.563497,114.530762],[-21.646428,114.971238],[-21.73,115.415115],[-21.81422,115.862432],[-21.631465,115.896691],[-21.448657,115.930662],[-21.265796,115.964345],[-21.183694,115.516634],[-21.001486,115.549899],[-20.819225,115.582877],[-20.636913,115.615567],[-20.45455,115.64797],[-20.375883,115.203198],[-20.194171,115.23519],[-20.012408,115.266895],[-19.830595,115.298313],[-19.75462,114.856584],[-19.573455,114.887596],[-19.392241,114.918323],[-19.210978,114.948764],[-19.137659,114.510055],[-18.957041,114.540094],[-18.776375,114.569849],[-18.704987,114.134249],[-18.524962,114.163607],[-18.344891,114.192681],[-18.275407,113.760159],[-18.095973,113.78884],[-17.916493,113.817238],[-17.848888,113.387765],[-17.781791,112.961521],[-17.959921,112.933337],[-17.892659,112.510391],[-18.070078,112.482032],[-18.002656,112.062349],[-18.179368,112.033817],[-18.356034,112.005007],[-18.532655,111.975918],[-18.709229,111.946551],[-18.885757,111.916906],[-19.062239,111.886982],[-19.238672,111.856779],[-19.415058,111.826299],[-31.590505,113.586986],[-31.769604,113.537023],[-31.948624,113.486778],[-32.07293,113.928333],[-32.252567,113.877609],[-32.432124,113.826602],[-32.6116,113.775311],[-32.738981,114.219718],[-32.919077,114.167943],[-33.09909,114.115885],[-33.228883,114.56337],[-33.40952,114.510822],[-33.541045,114.961623],[-33.72231,114.908582],[-33.90349,114.855256],[-34.084587,114.801644],[-34.2193,115.255376],[-34.401027,115.201265],[-34.537531,115.658384],[-34.675121,116.119145],[-34.813813,116.583591],[-34.953618,117.051768],[-35.094551,117.523721],[-34.90916,117.578922],[-34.723683,117.633831],[-34.538119,117.688448],[-34.67794,118.164888],[-34.491539,118.219432],[-34.352469,117.742772],[-34.166734,117.796803],[-34.305051,118.273682],[-34.118479,118.327637],[-33.931821,118.381299],[-33.74508,118.434665],[-33.558254,118.487738],[-33.371345,118.540515],[-33.184352,118.592998],[-32.997278,118.645185],[-32.810121,118.697078],[-32.622882,118.748675],[-32.435563,118.799977],[-32.248162,118.850984],[-32.060682,118.901695],[-31.931413,118.422284],[-32.118138,118.371777],[-32.304783,118.320976],[-32.491347,118.269881],[-32.677831,118.218492],[-32.864233,118.166808],[-32.732256,117.692274],[-32.601336,117.221535],[-32.471458,116.754547],[-32.342612,116.291265],[-32.214783,115.831645],[-32.087962,115.375644],[-31.962134,114.923219],[-31.83729,114.474328],[-31.713417,114.028931],[-65.769906,178.363754],[-66.051123,178.259806],[-66.332175,178.155415],[-66.613062,178.05058],[-66.893783,177.945303],[-67.174338,177.839583],[-67.454726,177.733421],[-67.734947,177.626817],[-68.014998,177.519771],[-68.294881,177.412284],[-68.574594,177.304355],[-68.854136,177.195985],[-69.133507,177.087175],[-69.412706,176.977924],[-69.691732,176.868232],[-69.970585,176.758101],[-70.249264,176.647531],[-70.527768,176.536521],[-70.806097,176.425071],[-71.084249,176.313183],[-71.362225,176.200857],[-71.640024,176.088092],[-71.917644,175.974889],[-72.36991,177.081537],[-72.827901,178.202192],[-73.291725,179.337121],[-73.761495,180.4866],[-74.237326,181.650908],[-74.719336,182.830336],[-75.207647,184.025179],[-75.702381,185.235743],[-76.203668,186.462339],[-76.711638,187.705287],[-76.415512,187.826036],[-76.119195,187.946318],[-75.82269,188.066132],[-75.525996,188.185478],[-75.229114,188.304357],[-74.932044,188.422767],[-74.634789,188.540708],[-74.337348,188.65818],[-73.8451,187.408922],[-73.549445,187.52515],[-73.253607,187.640912],[-72.957586,187.756207],[-72.661385,187.871035],[-72.365002,187.985396],[-72.068439,188.09929],[-71.771698,188.212715],[-71.474777,188.325673],[-71.177679,188.438162],[-70.880404,188.550182],[-70.582953,188.661733],[-70.118641,187.420669],[-69.822971,187.53102],[-69.527129,187.640905],[-69.231113,187.750324],[-68.934925,187.859275],[-68.638566,187.967759],[-68.342036,188.075775],[-68.045336,188.183324],[-67.748466,188.290404],[-67.451428,188.397016],[-67.154223,188.50316],[-66.85685,188.608835],[-66.559311,188.71404],[-66.261607,188.818777],[-65.82857,187.584797],[-65.401157,186.366842],[-64.979258,185.1646],[-64.562767,183.97777],[-64.151581,182.806058],[-63.7456,181.649175],[-63.459041,181.749483],[-63.172324,181.849338],[-62.885451,181.948742],[-62.59842,182.047692],[-62.311234,182.14619],[-62.023893,182.244235],[-61.736398,182.341826],[-61.348158,181.195139],[-61.633845,181.098161],[-61.919379,181.000733],[-62.204759,180.902854],[-62.489985,180.804526],[-62.775054,180.705748],[-63.059968,180.60652],[-63.344725,180.506844],[-63.629324,180.406718],[-63.913765,180.306143],[-64.198047,180.205121],[-64.48217,180.103649],[-64.766132,180.00173],[-65.049933,179.899364],[-65.333572,179.796549],[-65.617049,179.693288],[-65.900362,179.589579],[-66.183511,179.485424],[-60.776326,181.387742],[-61.062318,181.291666],[-61.448749,182.438964],[-61.160947,182.535648],[-53.968348,186.066917],[-54.261727,185.981572],[-54.609523,187.173638],[-54.314263,187.25953],[-48.693775,190.097736],[-48.993518,190.020705],[-49.29314,189.9432],[-49.592639,189.865224],[-49.914635,191.097986],[-50.24084,192.34686],[-50.571337,193.612166],[-50.906211,194.894229],[-51.245549,196.193384],[-50.936068,196.27396],[-50.62646,196.354047],[-50.316726,196.433646],[-50.006867,196.512756],[-49.696884,196.591378],[-49.386777,196.669511],[-49.076548,196.747154],[-48.766196,196.824308],[-48.455723,196.900973],[-48.145129,196.977148],[-47.834416,197.052833],[-47.523584,197.128028],[-47.212633,197.202732],[-46.901565,197.276946],[-46.59038,197.350669],[-46.27908,197.423902],[-45.967664,197.496643],[-45.656134,197.568893],[-45.344491,197.640652],[-45.648783,198.966956],[-45.334935,199.038701],[-45.032735,197.711919],[-44.720866,197.782695],[-45.020974,199.109952],[-44.706901,199.180707],[-44.392717,199.250967],[-44.096797,197.92277],[-43.784597,197.992069],[-43.472289,198.060875],[-43.159872,198.129189],[-42.847348,198.197011],[-42.534717,198.264339],[-42.820154,199.594828],[-42.505319,199.662112],[-42.221981,198.331174],[-41.90914,198.397516],[-41.631625,197.083765],[-41.942395,197.017863],[-42.253061,196.95147],[-42.563621,196.884588],[-42.874076,196.817216],[-42.592039,195.522503],[-42.900346,195.455088],[-43.208545,195.387186],[-43.516637,195.318799],[-43.824621,195.249926],[-44.132496,195.180567],[-44.440262,195.110723],[-44.747916,195.040393],[-44.455477,193.765754],[-44.76101,193.695402],[-45.066433,193.624568],[-45.371743,193.553253],[-45.67694,193.481456],[-45.982023,193.409178],[-46.286993,193.336419],[-46.591847,193.26318],[-46.289334,192.008355],[-46.592094,191.935113],[-46.894737,191.861394],[-47.197264,191.787198],[-47.499674,191.712524],[-47.801966,191.637374],[-48.104138,191.561747],[-48.406191,191.485643],[-48.708124,191.409064],[-49.009935,191.332008],[-26.909539,209.502526],[-27.239913,209.459826],[-27.430381,210.924415],[-27.097697,210.967413],[-125.448101,353.899715],[-126.006082,353.70143],[-126.563749,353.502265],[-127.121102,353.302222],[-127.678138,353.101299],[-128.234857,352.899498],[-128.791257,352.69682],[-129.347336,352.493264],[-129.903094,352.288831],[-130.458528,352.083522],[-131.013638,351.877338],[-131.568423,351.670278],[-133.212696,356.065271],[-134.898589,360.571506],[-134.329762,360.783807],[-133.760602,360.99521],[-135.475127,365.622397],[-134.898334,365.8356],[-134.321205,366.047894],[-133.743742,366.259277],[-133.165947,366.46975],[-132.58782,366.679311],[-132.009364,366.887959],[-131.430579,367.095696],[-130.851468,367.302519],[-130.272031,367.508428],[-128.623354,362.857373],[-127.015887,358.32257],[-51.99869,376.595586],[-52.592556,376.513111],[-53.186291,376.429698],[-53.779894,376.34535],[-54.373363,376.260065],[-54.966696,376.173845],[-55.559893,376.086689],[-56.152952,375.998598],[-56.745871,375.909571],[-57.464027,380.666949],[-58.200593,385.546285],[-58.808567,385.454017],[-59.416395,385.360791],[-60.024075,385.266606],[-60.631606,385.171462],[-61.238986,385.075361],[-61.846214,384.978302],[-62.453288,384.880285],[-63.264199,389.877683],[-62.649243,389.976973],[-62.034131,390.075292],[-61.418864,390.172641],[-60.803445,390.26902],[-60.187875,390.364428],[-59.572154,390.458865],[-58.956286,390.552331],[-58.340271,390.644826],[-57.724111,390.736348],[-57.107807,390.826899],[-56.491362,390.916478],[-55.874775,391.005085],[-55.25805,391.092719],[-54.641188,391.17938],[-54.024189,391.265069],[-53.331714,386.249887],[-52.656767,381.361646],[-67.392852,374.147435],[-67.982838,374.040684],[-68.572654,373.933003],[-69.1623,373.824391],[-69.751774,373.71485],[-70.341075,373.60438],[-70.9302,373.49298],[-71.519149,373.380651],[-72.107921,373.267394],[-72.696513,373.153208],[-73.284924,373.038094],[-74.212391,377.759131],[-75.163636,382.601196],[-74.56014,382.719261],[-73.956459,382.836374],[-73.352595,382.952535],[-72.748547,383.067743],[-72.144319,383.181999],[-71.539912,383.295301],[-70.935326,383.40765],[-70.330564,383.519046],[-69.725627,383.629488],[-69.120517,383.738975],[-68.245752,378.882511],[-63.060206,384.781311],[-63.666968,384.68138],[-64.493639,389.676196],[-63.878998,389.777424],[-93.464377,107.085667],[-93.633146,106.938131],[-93.801682,106.790329],[-94.242032,107.291654],[-94.072705,107.44015],[-93.903144,107.588379],[-92.194755,109.055889],[-92.366633,108.910352],[-92.538281,108.764545],[-92.974749,109.277546],[-92.802291,109.424041],[-92.629603,109.570264],[-90.187969,111.588603],[-90.363843,111.446229],[-90.792075,111.974369],[-90.615367,112.117419],[-88.297812,113.951554],[-88.477416,113.812158],[-88.656799,113.672478],[-89.078942,114.213734],[-88.898704,114.354079],[-88.718246,114.494139],[-86.352364,116.288882],[-86.535656,116.152551],[-86.718734,116.015931],[-87.133624,116.570988],[-86.949671,116.708262],[-86.765502,116.845246],[-64.046725,133.841909],[-64.257728,133.740734],[-64.468571,133.639227],[-64.679254,133.537387],[-64.889776,133.435215],[-65.100136,133.332711],[-65.419229,133.986251],[-65.207838,134.089258],[-64.996284,134.19193],[-64.784569,134.294269],[-64.572692,134.396274],[-64.360655,134.497945],[-67.465802,135.458099],[-67.67935,135.35153],[-68.017719,136.028233],[-68.232165,135.920793],[-68.575013,136.603757],[-68.359489,136.711737],[-68.704711,137.402144],[-68.921323,137.293619],[-69.271149,137.990484],[-69.624544,138.694459],[-69.981563,139.405654],[-70.201333,139.295112],[-70.563166,140.013068],[-70.342263,140.12418],[-70.7067,140.850151],[-70.484477,140.961488],[-70.851553,141.6956],[-71.222472,142.4374],[-70.997745,142.549548],[-70.627996,141.807164],[-70.262078,141.072474],[-69.899933,140.345356],[-69.541501,139.625696],[-69.186727,138.913379],[-68.835554,138.208293],[-68.487928,137.510328],[-68.143795,136.819377],[-67.803104,136.135335],[-64.014027,138.799579],[-64.232849,138.69845],[-64.55723,139.39889],[-64.884905,140.106441],[-65.215923,140.82121],[-65.550336,141.543311],[-65.888197,142.272855],[-66.229558,143.009958],[-66.574474,143.754739],[-66.923002,144.507318],[-67.275199,145.267819],[-67.631122,146.036366],[-67.400723,146.142846],[-67.046013,145.373738],[-66.81666,145.479296],[-66.466864,144.717688],[-66.238546,144.822333],[-65.893583,144.068114],[-65.552194,143.321709],[-65.214324,142.582999],[-64.879919,141.851865],[-65.103554,141.749366],[-64.77142,141.026214],[-64.442658,140.310404],[-64.663862,140.208597],[-64.337304,139.50053],[-83.813333,127.821923],[-84.014817,127.689582],[-84.4391,128.334426],[-84.86769,128.985816],[-85.300653,129.643853],[-85.738056,130.308638],[-86.179968,130.980277],[-86.626459,131.658874],[-87.0776,132.34454],[-87.533466,133.037385],[-87.994129,133.737522],[-87.783101,133.876132],[-87.323543,133.175269],[-87.113403,133.312821],[-86.659725,132.618542],[-86.210749,131.931457],[-86.002572,132.067256],[-85.559297,131.386554],[-85.766401,131.251454],[-85.326609,130.578425],[-84.891305,129.912264],[-84.46042,129.252865],[-84.66416,129.119501],[-84.236598,128.467436],[-115.195735,143.917977],[-115.422565,143.736122],[-115.649108,143.55391],[-115.875364,143.371341],[-116.101331,143.188415],[-116.32701,143.005133],[-116.552399,142.821495],[-116.777499,142.637503],[-117.002308,142.453155],[-117.226826,142.268453],[-117.451052,142.083397],[-118.167147,142.949674],[-118.392446,142.763134],[-118.617451,142.57624],[-118.842161,142.38899],[-119.066576,142.201387],[-119.290694,142.01343],[-119.514516,141.825119],[-120.247661,142.695126],[-120.472557,142.505305],[-120.697152,142.31513],[-120.921448,142.124601],[-121.145443,141.933719],[-121.89318,142.809766],[-122.118254,142.61735],[-122.343025,142.424579],[-122.567491,142.231454],[-122.791652,142.037976],[-123.015508,141.844144],[-123.239058,141.649959],[-124.004442,142.529685],[-124.229072,142.333939],[-124.453392,142.13784],[-124.677404,141.941388],[-124.901105,141.744582],[-125.124496,141.547423],[-125.906445,142.432006],[-126.130919,142.233261],[-126.355078,142.034162],[-126.578924,141.834711],[-126.802455,141.634906],[-127.02567,141.434749],[-127.824492,142.324186],[-128.048794,142.122416],[-128.272776,141.920293],[-128.49644,141.717817],[-128.719784,141.514989],[-128.942807,141.311808],[-129.758818,142.206096],[-129.98293,142.001276],[-130.206719,141.796102],[-130.430185,141.590576],[-130.653326,141.384698],[-131.485427,142.285145],[-131.709662,142.077602],[-131.933569,141.869706],[-132.157148,141.661456],[-132.380399,141.452855],[-133.228904,142.35951],[-133.453254,142.149217],[-133.677272,141.938571],[-133.900957,141.727571],[-134.12431,141.516219],[-134.347329,141.304515],[-134.570014,141.09246],[-135.438117,142.002639],[-135.661902,141.788862],[-135.885349,141.574733],[-136.108458,141.360252],[-136.331228,141.145418],[-137.216403,142.061851],[-137.440279,141.84527],[-137.663813,141.628336],[-137.887004,141.41105],[-138.109853,141.193412],[-138.332358,140.975422],[-139.236396,141.896733],[-139.460008,141.676967],[-139.683274,141.456847],[-139.906193,141.236376],[-140.128763,141.015554],[-140.350985,140.794381],[-141.274249,141.720562],[-141.497581,141.497581],[-142.434551,142.434551],[-143.384013,143.384013],[-144.346217,144.346217],[-145.321423,145.321423],[-146.309896,146.309896],[-147.311908,147.311908],[-147.079399,147.544051],[-146.078968,146.54046],[-145.847677,146.77066],[-145.616023,147.000494],[-145.384007,147.229963],[-145.151629,147.459065],[-144.170982,146.462829],[-143.939815,146.690019],[-143.708291,146.916845],[-143.476409,147.143305],[-143.24417,147.3694],[-143.011575,147.595127],[-142.778624,147.820488],[-141.820482,146.828511],[-141.588742,147.051995],[-141.35665,147.275112],[-141.124206,147.497863],[-140.891411,147.720247],[-140.658265,147.942264],[-139.720644,146.956088],[-139.488706,147.176259],[-139.25642,147.396064],[-139.023788,147.615503],[-138.79081,147.834574],[-138.557487,148.053278],[-137.639985,147.072897],[-137.407865,147.289787],[-137.175403,147.50631],[-136.942599,147.722467],[-136.709455,147.938256],[-136.475971,148.153677],[-135.578198,147.179085],[-135.345913,147.392723],[-135.113291,147.605994],[-134.880333,147.818899],[-134.647039,148.031435],[-134.413411,148.243603],[-133.534985,147.274793],[-133.302551,147.485208],[-133.069786,147.695257],[-132.836689,147.904938],[-132.603263,148.114252],[-131.742293,147.152571],[-131.510054,147.36016],[-131.277488,147.567382],[-131.044596,147.774236],[-130.811377,147.980723],[-129.967521,147.026108],[-129.735484,147.230898],[-129.503124,147.435321],[-129.270442,147.639378],[-128.441871,146.693069],[-128.210361,146.895453],[-127.978532,147.097471],[-127.746385,147.299124],[-127.51392,147.50041],[-127.281138,147.701329],[-126.470513,146.760653],[-126.238899,146.959928],[-126.006971,147.158837],[-125.77473,147.35738],[-124.978768,146.424834],[-124.747686,146.621756],[-124.516293,146.818314],[-124.28459,147.014506],[-123.503005,146.089981],[-123.272453,146.284576],[-123.041593,146.478808],[-122.810428,146.672675],[-122.578957,146.866177],[-122.347181,147.059314],[-121.582589,146.140286],[-121.351959,146.331853],[-121.121027,146.523056],[-120.368798,145.613066],[-120.139002,145.802719],[-119.908906,145.992009],[-119.678512,146.180936],[-118.93983,145.278675],[-118.710562,145.466075],[-118.480999,145.653113],[-117.754194,144.759624],[-117.525747,144.945154],[-117.297007,145.130324],[-117.067975,145.315133],[-116.354216,144.429153],[-116.126292,144.612476],[-115.898079,144.795439],[-85.819684,166.995683],[-86.082947,166.860129],[-86.61757,167.896424],[-86.352673,168.03282],[-86.60883,166.587776],[-86.871449,166.450977],[-87.133851,166.313765],[-87.675001,167.346666],[-87.410969,167.484731],[-87.146719,167.622379],[-87.396037,166.176139],[-87.658005,166.0381],[-88.20241,167.069289],[-87.938815,167.208186],[-72.297614,174.541879],[-72.572794,174.427641],[-73.026329,175.517704],[-72.749428,175.632656],[-72.847795,174.31297],[-73.122614,174.197864],[-73.579584,175.286491],[-73.303047,175.402316],[-91.572525,172.135538],[-91.843886,171.990905],[-92.436366,173.100408],[-93.036539,174.224319],[-93.311193,174.077374],[-93.921006,175.215015],[-94.538842,176.367623],[-94.816874,176.218306],[-95.444734,177.38519],[-96.080964,178.567631],[-96.362464,178.415879],[-97.009122,179.613171],[-97.29227,179.459954],[-97.949578,180.67239],[-98.234396,180.517688],[-98.902584,181.745565],[-98.615829,181.901319],[-99.291205,183.14708],[-99.579924,182.99026],[-100.266605,184.252121],[-99.975896,184.410023],[-99.684938,184.567466],[-99.393732,184.72445],[-99.102278,184.880975],[-98.810579,185.037039],[-98.133869,183.769802],[-97.843922,183.924341],[-97.178391,182.673293],[-96.521851,181.439148],[-95.874124,180.221567],[-95.235032,179.020219],[-94.604403,177.834782],[-93.982072,176.66494],[-93.367875,175.510389],[-92.761654,174.370831],[-92.163254,173.245975],[-108.120109,163.762862],[-108.378246,163.592142],[-109.081927,164.654317],[-109.794805,165.730376],[-110.517063,166.820592],[-111.248886,167.925246],[-111.990465,169.044627],[-112.741998,170.179032],[-113.503685,171.328765],[-114.275734,172.494139],[-115.058358,173.675475],[-115.851776,174.873104],[-115.575839,175.055597],[-114.784311,173.856718],[-114.509978,174.037529],[-113.731084,172.85373],[-112.962715,171.685926],[-112.691808,171.863867],[-111.935569,170.710543],[-111.189412,169.572595],[-110.453137,168.449718],[-110.718662,168.275312],[-109.990327,167.168355],[-109.271512,166.075867],[-108.562031,164.997565],[-108.822114,164.826146],[-121.139538,182.229884],[-121.426783,182.038608],[-121.713726,181.846879],[-122.000366,181.654697],[-122.286703,181.462064],[-122.572735,181.26898],[-122.858463,181.075444],[-123.143885,180.881459],[-123.429,180.687023],[-124.323309,181.996196],[-124.036127,182.192041],[-123.748637,182.387432],[-123.460839,182.58237],[-123.172735,182.776853],[-122.884323,182.970882],[-122.595606,183.164456],[-122.306584,183.357574],[-122.017258,183.550236],[-208.760162,290.597869],[-209.218205,290.268272],[-211.70842,293.723183],[-212.171389,293.388931],[-214.727174,296.923051],[-217.345283,300.543352],[-220.028024,304.253025],[-219.547912,304.599653],[-219.067253,304.945525],[-218.58605,305.290637],[-218.104303,305.63499],[-217.622014,305.978584],[-217.139183,306.321416],[-216.655812,306.663486],[-216.171902,307.004793],[-215.687455,307.345337],[-215.202471,307.685116],[-214.716952,308.02413],[-214.230899,308.362378],[-213.744313,308.699859],[-213.257195,309.036572],[-212.769547,309.372517],[-210.175307,305.600423],[-207.643566,301.919206],[-205.172094,298.325619],[-205.642329,298.001671],[-206.112053,297.676981],[-206.581264,297.35155],[-207.049962,297.02538],[-207.518144,296.698472],[-207.98581,296.370825],[-208.452959,296.042441],[-208.91959,295.713321],[-209.385701,295.383465],[-209.851291,295.052875],[-210.316359,294.721551],[-210.780904,294.389493],[-211.244925,294.056704],[-193.857977,321.560755],[-194.364871,321.254621],[-196.793942,325.269494],[-196.280714,325.579454],[-105.530954,50.49922],[-105.610465,50.332724],[-106.018202,50.527046],[-105.938384,50.694185],[-105.290369,52.026722],[-105.372289,51.860604],[-105.780684,52.061601],[-105.698446,52.228364],[-102.983657,67.526785],[-103.090026,67.364285],[-103.509063,67.638106],[-103.402262,67.801267],[-102.737756,69.706872],[-102.847563,69.544757],[-103.269042,69.829758],[-103.158785,69.992537],[-101.185161,83.37488],[-101.316526,83.215197],[-101.755095,83.575411],[-101.623161,83.735785],[-100.757441,86.550862],[-100.893815,86.391849],[-101.3363,86.770734],[-101.199328,86.930444],[-100.510697,87.725742],[-100.648924,87.567118],[-101.09228,87.952848],[-100.953444,88.112172],[-99.874928,92.002629],[-100.019902,91.845002],[-100.468389,92.256833],[-100.322765,92.415167],[-98.996469,95.619896],[-99.147149,95.463649],[-99.597784,95.897543],[-99.44642,96.0545],[-141.497581,141.497581],[-141.720562,141.274249],[-141.94319,141.050565],[-142.165465,140.82653],[-142.387386,140.602146],[-142.608953,140.377411],[-143.553282,141.306963],[-143.775959,141.080389],[-143.998279,140.853464],[-144.220241,140.626189],[-144.441843,140.398563],[-144.663087,140.170589],[-144.883971,139.942266],[-145.84976,140.875114],[-146.071753,140.644919],[-146.293383,140.414373],[-146.514649,140.183479],[-146.735551,139.952236],[-146.956088,139.720644],[-147.176259,139.488706],[-148.163912,140.42477],[-148.385193,140.190926],[-148.606104,139.956732],[-148.826645,139.722191],[-149.046817,139.487302],[-149.266617,139.252066],[-149.486047,139.016484],[-149.705104,138.780556],[-150.716515,139.71816],[-150.936678,139.480291],[-151.156465,139.242075],[-151.375876,139.003512],[-151.594911,138.764604],[-151.813569,138.52535],[-152.031849,138.285752],[-152.249751,138.04581],[-153.28535,138.984794],[-153.504352,138.742874],[-153.722973,138.500609],[-153.941212,138.258],[-154.159068,138.015047],[-154.37654,137.77175],[-154.593629,137.528111],[-154.810333,137.28413],[-155.026651,137.039807],[-156.088361,137.978332],[-156.305773,137.731993],[-156.522796,137.485311],[-156.73943,137.238288],[-156.955674,136.990922],[-157.171528,136.743217],[-157.386991,136.495171],[-157.602062,136.246785],[-157.816741,135.998061],[-158.905012,136.935874],[-159.120776,136.685094],[-159.336145,136.433974],[-159.551117,136.182515],[-159.765693,135.930717],[-159.979871,135.678581],[-160.193651,135.426107],[-160.407033,135.173297],[-160.620016,134.92015],[-160.832599,134.666668],[-161.949367,135.601748],[-162.163024,135.346168],[-162.376277,135.090252],[-162.589127,134.834],[-162.801572,134.577412],[-163.013612,134.32049],[-163.225247,134.063233],[-163.436475,133.805643],[-163.647298,133.547721],[-163.857713,133.289466],[-165.003442,134.221455],[-164.791555,134.481515],[-164.579259,134.741242],[-164.366553,135.000633],[-165.523933,135.951233],[-166.697727,136.915316],[-167.888288,137.89317],[-169.095977,138.885092],[-168.876731,139.151602],[-168.657064,139.417765],[-168.436978,139.683581],[-168.216473,139.94905],[-167.99555,140.214171],[-167.774208,140.478943],[-167.55245,140.743366],[-167.330274,141.007438],[-167.107683,141.27116],[-165.914194,140.262197],[-165.69278,140.523686],[-165.470953,140.784826],[-165.248715,141.045616],[-165.026066,141.306055],[-164.803006,141.566143],[-164.579537,141.825878],[-164.355658,142.085261],[-164.13137,142.34429],[-163.906675,142.602965],[-163.681571,142.861286],[-163.45606,143.119251],[-162.29693,142.104337],[-162.072615,142.360119],[-161.847897,142.615548],[-161.622776,142.870621],[-161.397253,143.12534],[-161.171329,143.379702],[-160.945003,143.633707],[-160.718278,143.887356],[-160.491153,144.140646],[-160.263628,144.393578],[-160.035705,144.646151],[-158.908821,143.627632],[-158.682108,143.878069],[-158.455,144.128148],[-158.227498,144.377869],[-157.999602,144.627231],[-157.771313,144.876233],[-157.542632,145.124874],[-157.313559,145.373155],[-157.084095,145.621074],[-156.85424,145.868631],[-155.757481,144.848686],[-155.528846,145.094151],[-155.299824,145.339256],[-155.070416,145.583999],[-154.840622,145.82838],[-154.610443,146.072399],[-154.379879,146.316054],[-153.307917,145.300084],[-153.078572,145.541686],[-152.848848,145.782926],[-152.618743,146.023803],[-152.388258,146.264317],[-152.157395,146.504467],[-151.926153,146.744253],[-150.878503,145.732336],[-150.64848,145.970106],[-150.418083,146.207513],[-150.187311,146.444556],[-149.956166,146.681235],[-149.724648,146.917549],[-149.492757,147.153498],[-148.468947,146.145708],[-148.238276,146.379678],[-148.007236,146.613283],[-147.775827,146.846523],[-147.544051,147.079399],[-147.311908,147.311908],[-146.309896,146.309896],[-145.321423,145.321423],[-144.346217,144.346217],[-143.384013,143.384013],[-142.434551,142.434551],[-192.760385,106.875322],[-192.928699,106.571186],[-194.336772,107.348986],[-194.16723,107.655342],[-193.096533,106.266785],[-193.263887,105.962119],[-194.674406,106.735474],[-194.505831,107.042363],[-200.71774,94.884005],[-200.867133,94.567334],[-201.016025,94.250428],[-201.164418,93.933288],[-202.643393,94.623892],[-202.493909,94.943364],[-202.343922,95.2626],[-202.193431,95.581599],[-257.21766,133.212338],[-257.42743,132.806513],[-257.636559,132.400358],[-257.845048,131.993874],[-258.052896,131.587061],[-258.260101,131.179921],[-258.466664,130.772455],[-260.951535,132.029687],[-261.159435,131.617975],[-261.366686,131.205936],[-261.573286,130.79357],[-261.779236,130.380879],[-261.984535,129.967864],[-262.189182,129.554526],[-262.393177,129.140865],[-262.596519,128.726883],[-262.799208,128.312581],[-263.001244,127.89796],[-265.554254,129.139493],[-265.75759,128.720526],[-265.960265,128.301238],[-266.162279,127.881632],[-266.36363,127.461707],[-266.56432,127.041465],[-266.764346,126.620908],[-266.963708,126.200035],[-267.162407,125.778848],[-267.360441,125.357349],[-269.981207,126.586148],[-270.180511,126.160203],[-270.379143,125.733943],[-270.577102,125.30737],[-270.774388,124.880486],[-270.971001,124.453292],[-271.16694,124.025787],[-271.362204,123.597975],[-271.556794,123.169854],[-274.245046,124.389163],[-274.440879,123.956496],[-274.63603,123.52352],[-274.830498,123.090236],[-275.024282,122.656647],[-275.217383,122.222753],[-275.409798,121.788554],[-275.601529,121.354053],[-275.792574,120.919249],[-275.982934,120.484145],[-278.742318,121.688793],[-278.933887,121.249036],[-279.124763,120.808977],[-279.314944,120.368618],[-279.50443,119.92796],[-279.693222,119.487003],[-279.881317,119.045749],[-280.068717,118.604199],[-282.897233,119.802026],[-283.085821,119.355719],[-283.273706,118.909114],[-283.460885,118.462214],[-283.64736,118.01502],[-283.833129,117.567532],[-286.728909,118.767003],[-289.684386,119.991201],[-292.701425,121.2409],[-292.509851,121.70237],[-292.31755,122.163537],[-292.124522,122.6244],[-291.930767,123.084958],[-291.736286,123.54521],[-291.54108,124.005155],[-291.345148,124.464792],[-291.148492,124.924119],[-290.951111,125.383135],[-290.753007,125.841839],[-290.55418,126.30023],[-290.35463,126.758307],[-290.154358,127.216069],[-289.953364,127.673515],[-289.751649,128.130642],[-289.549213,128.587452],[-289.346058,129.043941],[-289.142182,129.500109],[-288.937587,129.955956],[-288.732274,130.411479],[-288.526242,130.866677],[-288.319493,131.32155],[-288.112027,131.776097],[-287.903844,132.230316],[-287.694945,132.684206],[-287.48533,133.137765],[-287.275001,133.590994],[-290.298435,134.996976],[-290.085169,135.454639],[-289.871183,135.911965],[-289.656475,136.368953],[-289.441046,136.825602],[-289.224898,137.281911],[-289.008031,137.737878],[-288.790444,138.193502],[-288.57214,138.648783],[-288.353117,139.103719],[-288.133378,139.558309],[-287.912921,140.012552],[-287.691749,140.466446],[-287.469861,140.919991],[-287.247258,141.373186],[-287.02394,141.826029],[-286.799909,142.278519],[-286.575164,142.730655],[-286.349707,143.182437],[-286.123537,143.633862],[-285.896656,144.08493],[-285.669063,144.53564],[-285.44076,144.98599],[-285.211747,145.435979],[-284.982025,145.885607],[-284.751594,146.334872],[-284.520454,146.783773],[-284.288607,147.232309],[-281.327765,145.698896],[-278.427961,144.197096],[-275.587327,142.725939],[-272.80407,141.284497],[-270.076469,139.87188],[-267.402872,138.487231],[-264.781689,137.129728],[-262.211396,135.79858],[-259.690523,134.493027],[-269.684841,120.275337],[-269.874193,119.849867],[-270.062873,119.424098],[-270.250881,118.998032],[-270.438217,118.57167],[-270.624881,118.145014],[-270.810871,117.718063],[-270.996188,117.29082],[-271.180831,116.863285],[-271.364799,116.435459],[-271.548093,116.007344],[-271.73071,115.57894],[-271.912653,115.150249],[-272.093918,114.721271],[-272.274507,114.292008],[-272.454419,113.86246],[-272.633653,113.43263],[-275.30611,114.544539],[-275.486416,114.11021],[-278.213569,115.239833],[-278.031477,115.678462],[-277.848695,116.116803],[-277.665221,116.554854],[-277.481056,116.992616],[-277.296202,117.430087],[-277.110657,117.867266],[-276.924424,118.304152],[-276.737502,118.740744],[-276.549891,119.17704],[-273.839046,118.008822],[-273.652593,118.440548],[-273.46546,118.871979],[-273.277646,119.303115],[-273.089153,119.733954],[-272.899981,120.164495],[-272.710129,120.594737],[-272.5196,121.02468],[-272.328392,121.454321],[-290.510978,134.538978],[-290.722799,134.080644],[-290.933896,133.621977],[-291.14427,133.162978],[-291.35392,132.703648],[-291.562845,132.243987],[-291.771045,131.783998],[-291.978519,131.323681],[-292.185267,130.863037],[-292.391289,130.402068],[-292.596583,129.940774],[-292.801149,129.479157],[-293.004987,129.017218],[-293.208096,128.554958],[-293.410476,128.092379],[-293.612126,127.629481],[-293.813046,127.166265],[-294.013235,126.702733],[-294.212693,126.238886],[-294.411419,125.774725],[-294.609412,125.310251],[-294.806673,124.845466],[-295.003201,124.38037],[-295.198995,123.914964],[-295.394054,123.44925],[-295.588379,122.98323],[-295.781969,122.516903],[-298.928046,123.820051],[-302.141769,125.151218],[-305.425343,126.511319],[-305.225441,126.992849],[-305.024781,127.474064],[-304.823362,127.954961],[-304.621184,128.43554],[-304.418249,128.9158],[-304.214557,129.395739],[-304.010108,129.875356],[-303.804903,130.35465],[-307.142827,131.786865],[-306.934603,132.271097],[-306.725616,132.755],[-306.515866,133.238573],[-306.305354,133.721815],[-306.09408,134.204724],[-305.882044,134.6873],[-305.669248,135.16954],[-305.455692,135.651444],[-305.241375,136.133011],[-305.0263,136.614239],[-304.810466,137.095127],[-304.593873,137.575675],[-304.376523,138.05588],[-304.158416,138.535742],[-303.939553,139.015259],[-303.719933,139.49443],[-303.499558,139.973255],[-303.278428,140.451731],[-303.056544,140.929858],[-302.833906,141.407634],[-302.610515,141.885059],[-302.386371,142.362131],[-302.161475,142.838849],[-301.935828,143.315211],[-301.709429,143.791217],[-301.48228,144.266865],[-301.254382,144.742155],[-304.601053,146.350113],[-304.369864,146.830319],[-304.137919,147.310159],[-303.905218,147.789633],[-303.67176,148.268739],[-303.437547,148.747477],[-303.202579,149.225844],[-302.966858,149.703841],[-302.730382,150.181465],[-302.493154,150.658716],[-302.255173,151.135591],[-302.016441,151.612091],[-301.776957,152.088214],[-301.536723,152.563959],[-301.295739,153.039324],[-301.054005,153.514308],[-300.811523,153.988911],[-300.568292,154.46313],[-300.324314,154.936966],[-300.079589,155.410416],[-299.834117,155.883479],[-299.5879,156.356155],[-299.340937,156.828442],[-299.09323,157.300339],[-298.844779,157.771844],[-298.595585,158.242957],[-298.345648,158.713677],[-298.094969,159.184002],[-297.843549,159.65393],[-297.591387,160.123462],[-300.934505,161.922276],[-300.678762,162.39668],[-300.422272,162.87068],[-300.165034,163.344274],[-299.90705,163.817463],[-299.64832,164.290243],[-299.388844,164.762616],[-299.128624,165.234578],[-298.86766,165.70613],[-298.605953,166.177269],[-298.343502,166.647995],[-298.08031,167.118307],[-297.816377,167.588202],[-297.551702,168.057681],[-297.286288,168.526742],[-297.020134,168.995384],[-296.753241,169.463606],[-296.48561,169.931406],[-296.217242,170.398783],[-295.948137,170.865737],[-295.678296,171.332265],[-295.407719,171.798367],[-295.136408,172.264043],[-294.864363,172.729289],[-294.591584,173.194106],[-294.318072,173.658492],[-294.043829,174.122447],[-293.768854,174.585968],[-293.493148,175.049055],[-293.216713,175.511706],[-292.939548,175.973921],[-292.661654,176.435699],[-295.986746,178.440282],[-295.704959,178.906862],[-295.422436,179.372997],[-295.139179,179.838686],[-294.855187,180.303928],[-294.570463,180.768721],[-294.285005,181.233064],[-293.998816,181.696957],[-293.711895,182.160398],[-293.424244,182.623385],[-293.135863,183.085919],[-292.846753,183.547997],[-292.556914,184.009619],[-292.266348,184.470782],[-291.975055,184.931487],[-291.683036,185.391732],[-291.390291,185.851516],[-291.096822,186.310838],[-290.802628,186.769696],[-290.507711,187.22809],[-290.212072,187.686018],[-289.91571,188.143479],[-289.618628,188.600473],[-289.320825,189.056997],[-289.022303,189.513051],[-288.723061,189.968633],[-288.423102,190.423743],[-288.122425,190.87838],[-287.821032,191.332542],[-287.518923,191.786227],[-287.216098,192.239436],[-290.516821,194.448675],[-290.209794,194.906609],[-289.902045,195.364057],[-289.593575,195.82102],[-289.284385,196.277496],[-288.974475,196.733483],[-288.663846,197.188981],[-285.384176,194.948608],[-282.178194,192.758571],[-279.043442,190.617193],[-275.977574,188.52287],[-276.274551,188.08739],[-276.570841,187.651442],[-276.866443,187.215028],[-277.161356,186.778148],[-277.45558,186.340803],[-277.749114,185.902995],[-278.041957,185.464725],[-278.334108,185.025993],[-278.625567,184.586801],[-278.916333,184.14715],[-279.206406,183.707041],[-279.495783,183.266475],[-279.784466,182.825453],[-280.072453,182.383977],[-280.359743,181.942046],[-280.646336,181.499664],[-280.932231,181.056829],[-281.217427,180.613545],[-281.501924,180.169811],[-281.78572,179.725629],[-282.068816,179.281],[-282.35121,178.835925],[-279.282713,176.892397],[-279.561343,176.451719],[-279.839278,176.010603],[-280.116517,175.569048],[-280.39306,175.127057],[-280.668904,174.68463],[-280.944051,174.241769],[-281.218499,173.798474],[-281.492248,173.354747],[-281.765296,172.910589],[-282.037644,172.466001],[-282.30929,172.020983],[-282.580234,171.575538],[-282.850475,171.129667],[-283.120012,170.683369],[-283.388846,170.236647],[-283.656974,169.789502],[-283.924397,169.341934],[-284.191114,168.893945],[-284.457124,168.445536],[-284.722426,167.996708],[-284.98702,167.547462],[-285.250906,167.0978],[-285.514082,166.647721],[-285.776547,166.197229],[-286.038302,165.746323],[-286.299346,165.295004],[-286.559677,164.843275],[-286.819296,164.391136],[-287.078201,163.938587],[-283.991874,162.176112],[-284.247289,161.728026],[-284.501998,161.279537],[-284.755999,160.830647],[-285.009291,160.381358],[-285.261875,159.931669],[-285.513749,159.481582],[-285.764913,159.031099],[-286.015366,158.58022],[-286.265108,158.128947],[-286.514138,157.67728],[-286.762455,157.225222],[-287.010059,156.772772],[-287.256949,156.319932],[-287.503124,155.866704],[-287.748585,155.413087],[-287.99333,154.959085],[-288.237358,154.504697],[-288.48067,154.049924],[-288.723264,153.594768],[-288.96514,153.139231],[-289.206297,152.683312],[-289.446734,152.227014],[-289.686452,151.770337],[-289.92545,151.313283],[-290.163726,150.855852],[-290.40128,150.398046],[-287.312435,148.798341],[-287.546748,148.345034],[-287.780346,147.891359],[-288.013228,147.437315],[-288.245394,146.982905],[-288.476843,146.528129],[-288.707574,146.072989],[-288.937588,145.617486],[-289.166882,145.16162],[-289.395458,144.705393],[-289.623313,144.248806],[-289.850448,143.791861],[-290.076863,143.334558],[-290.302556,142.876898],[-290.527526,142.418883],[-290.751774,141.960514],[-290.975299,141.501791],[-291.1981,141.042717],[-291.420177,140.583292],[-291.641529,140.123517],[-291.862156,139.663394],[-292.082057,139.202923],[-292.301231,138.742106],[-292.519678,138.280944],[-292.737398,137.819438],[-292.95439,137.357589],[-293.170652,136.895399],[-293.386186,136.432868],[-293.60099,135.969998],[-273.207187,198.891905],[-273.520521,198.460781],[-273.833174,198.029164],[-274.145146,197.597054],[-274.456436,197.164453],[-274.767044,196.731362],[-275.076968,196.297781],[-275.386208,195.863712],[-275.694763,195.429155],[-278.791895,197.624591],[-281.959405,199.869913],[-285.199716,202.166842],[-284.880524,202.616381],[-284.560622,203.065415],[-284.240013,203.513944],[-283.918697,203.961967],[-283.596675,204.409483],[-283.273947,204.85649],[-282.950515,205.302988],[-282.626378,205.748975],[-279.415304,203.411347],[-276.276375,201.12624],[-108.127459,38.520391],[-108.188075,38.349815],[-108.597854,38.495071],[-108.537008,38.666293],[-108.3085,38.008377],[-108.368309,37.837516],[-108.427848,37.666561],[-108.487117,37.495512],[-108.898028,37.637532],[-108.838534,37.809229],[-108.77877,37.980831],[-108.718735,38.152339],[-110.036582,32.669841],[-110.087969,32.496261],[-110.139082,32.322601],[-110.189922,32.14886],[-110.607282,32.270628],[-110.55625,32.445027],[-110.504944,32.619346],[-110.453362,32.793583],[-110.240487,31.975039],[-110.290777,31.801138],[-110.340794,31.627159],[-110.390536,31.453101],[-110.808657,31.572234],[-110.758726,31.746951],[-110.70852,31.92159],[-110.658039,32.096149],[-112.17788,26.296153],[-112.219212,26.119204],[-112.260265,25.94219],[-112.301039,25.765112],[-112.728013,25.863072],[-112.687084,26.040823],[-112.645875,26.21851],[-112.604385,26.396132],[-112.421684,25.233494],[-112.46134,25.056162],[-112.500717,24.878767],[-112.92845,24.973357],[-112.888924,25.151426],[-112.849117,25.329433],[-112.617166,24.346214],[-112.655423,24.168575],[-113.083744,24.260465],[-113.045342,24.43878],[-106.852982,44.259954],[-106.922652,44.091381],[-106.992056,43.922698],[-107.400397,44.090332],[-107.330728,44.259658],[-107.260793,44.428875],[-113.9208,19.963833],[-113.952144,19.784143],[-113.983204,19.604404],[-114.418227,19.679225],[-114.387049,19.85965],[-114.355586,20.040026],[-287.902732,31.913448],[-287.952705,31.459356],[-288.001962,31.005185],[-288.050502,30.550938],[-288.098326,30.096614],[-288.145433,29.642216],[-288.191824,29.187743],[-288.237497,28.733199],[-288.282454,28.278582],[-288.326694,27.823896],[-288.370216,27.36914],[-288.413022,26.914316],[-288.45511,26.459425],[-288.49648,26.004469],[-291.270055,26.254473],[-294.097477,26.509331],[-296.980329,26.769185],[-299.920259,27.034184],[-302.918978,27.304482],[-302.875539,27.782183],[-302.831347,28.259815],[-302.786402,28.737376],[-302.740704,29.214866],[-302.694252,29.692284],[-302.647048,30.169627],[-302.599091,30.646895],[-305.65515,30.956409],[-305.605948,31.438421],[-305.555986,31.920354],[-305.505265,32.402208],[-305.453783,32.883981],[-305.401542,33.365673],[-305.348541,33.847282],[-305.29478,34.328806],[-305.24026,34.810245],[-305.184981,35.291597],[-305.128943,35.772862],[-305.072146,36.254037],[-305.014591,36.735123],[-304.956276,37.216117],[-304.897203,37.697018],[-304.837372,38.177826],[-304.776782,38.658539],[-304.715435,39.139156],[-304.653329,39.619675],[-304.590466,40.100096],[-304.526845,40.580417],[-304.462467,41.060637],[-304.397332,41.540755],[-304.331439,42.020769],[-304.264789,42.500679],[-307.369021,42.934288],[-307.300927,43.418988],[-307.232069,43.903579],[-307.162446,44.388062],[-307.092059,44.872434],[-307.020909,45.356694],[-306.948995,45.840842],[-306.876317,46.324875],[-306.802877,46.808793],[-306.728673,47.292595],[-306.653706,47.77628],[-306.577976,48.259845],[-306.501484,48.74329],[-306.42423,49.226614],[-306.346213,49.709816],[-306.267435,50.192894],[-306.187895,50.675847],[-306.107593,51.158674],[-306.026529,51.641374],[-305.944705,52.123946],[-305.86212,52.606388],[-305.778774,53.088699],[-308.930608,53.635914],[-308.845634,54.123063],[-308.759893,54.610077],[-308.673383,55.096956],[-308.586105,55.583697],[-308.49806,56.070301],[-308.409248,56.556765],[-308.319668,57.043088],[-308.229322,57.529269],[-308.138209,58.015307],[-308.04633,58.501201],[-307.953684,58.986949],[-307.860273,59.472551],[-307.766095,59.958005],[-307.671153,60.443309],[-307.575445,60.928464],[-307.478972,61.413466],[-307.381734,61.898316],[-307.283731,62.383012],[-307.184965,62.867553],[-307.085434,63.351938],[-306.985139,63.836165],[-306.884081,64.320233],[-306.78226,64.804141],[-309.977372,65.479071],[-309.873719,65.967856],[-309.769295,66.456477],[-309.664101,66.944933],[-309.558137,67.433222],[-309.451403,67.921343],[-309.343899,68.409296],[-309.235626,68.897078],[-309.126583,69.38469],[-309.016772,69.872128],[-308.906192,70.359393],[-308.794844,70.846482],[-308.682728,71.333396],[-308.569844,71.820132],[-308.456192,72.30669],[-308.341773,72.793067],[-308.226587,73.279264],[-308.110635,73.765278],[-307.993916,74.251109],[-307.876432,74.736755],[-307.758181,75.222215],[-307.639165,75.707488],[-307.519384,76.192573],[-307.398838,76.677468],[-307.277527,77.162173],[-307.155452,77.646686],[-307.032613,78.131005],[-306.909011,78.61513],[-306.784645,79.09906],[-306.659516,79.582793],[-306.533624,80.066328],[-306.40697,80.549664],[-306.279554,81.032799],[-303.122558,80.197549],[-302.995701,80.675505],[-302.86809,81.15326],[-302.739727,81.630814],[-302.61061,82.108164],[-302.48074,82.585311],[-302.350118,83.062252],[-302.218745,83.538986],[-302.086619,84.015512],[-301.953742,84.49183],[-301.820114,84.967937],[-298.740824,84.10106],[-298.607816,84.572101],[-298.474066,85.042931],[-298.339573,85.51355],[-298.204338,85.983957],[-298.068362,86.454149],[-297.931644,86.924126],[-294.922724,86.046248],[-295.058061,85.581017],[-295.192664,85.115573],[-295.326533,84.649918],[-295.459668,84.184052],[-295.592067,83.717977],[-295.723731,83.251693],[-295.85466,82.785202],[-295.984853,82.318506],[-296.11431,81.851604],[-296.24303,81.3845],[-296.371014,80.917192],[-296.49826,80.449684],[-296.624769,79.981975],[-296.75054,79.514067],[-296.875573,79.045962],[-296.999867,78.57766],[-297.123423,78.109163],[-294.152668,77.328197],[-294.274257,76.864191],[-294.395113,76.399995],[-294.515238,75.935608],[-294.63463,75.471032],[-294.753289,75.006269],[-294.871216,74.541319],[-294.988408,74.076184],[-295.104867,73.610864],[-295.220592,73.145362],[-295.335583,72.679677],[-295.449839,72.213812],[-295.56336,71.747767],[-295.676147,71.281543],[-295.788197,70.815143],[-295.899512,70.348566],[-296.010091,69.881814],[-296.119934,69.414888],[-296.22904,68.94779],[-293.296548,68.265248],[-293.403844,67.802604],[-293.510411,67.339791],[-293.616248,66.876811],[-293.721355,66.413664],[-293.825731,65.950352],[-293.929376,65.486877],[-294.03229,65.023238],[-294.134473,64.559438],[-294.235924,64.095477],[-294.336643,63.631356],[-294.43663,63.167078],[-294.535885,62.702642],[-294.634408,62.23805],[-294.732197,61.773303],[-294.829253,61.308403],[-294.925576,60.843351],[-295.021166,60.378147],[-295.116022,59.912792],[-295.210143,59.447289],[-295.303531,58.981638],[-292.408856,58.403478],[-292.500601,57.942246],[-292.591618,57.48087],[-292.681907,57.019352],[-292.771469,56.557691],[-292.860302,56.095889],[-292.948407,55.633948],[-293.035783,55.171869],[-293.12243,54.709653],[-293.208349,54.2473],[-293.293538,53.784812],[-293.377997,53.322191],[-293.461727,52.859437],[-293.544727,52.396552],[-293.626997,51.933536],[-293.708536,51.470391],[-293.789345,51.007118],[-293.869423,50.543718],[-293.94877,50.080193],[-291.095346,49.594053],[-291.173199,49.134904],[-291.250327,48.675633],[-291.326732,48.21624],[-291.402411,47.756727],[-291.477366,47.297096],[-291.551596,46.837347],[-291.625101,46.377482],[-291.697881,45.917501],[-291.769934,45.457406],[-291.841263,44.997198],[-291.911865,44.536878],[-291.981741,44.076447],[-292.050891,43.615906],[-292.119315,43.155258],[-292.187012,42.694501],[-292.253982,42.233639],[-292.320226,41.772671],[-292.385742,41.3116],[-292.450531,40.850426],[-289.638943,40.457694],[-289.702388,40.000853],[-289.765114,39.543913],[-289.827118,39.086874],[-289.888402,38.629738],[-289.948964,38.172505],[-290.008806,37.715178],[-290.067926,37.257757],[-290.126325,36.800244],[-290.184002,36.342638],[-290.240957,35.884943],[-290.29719,35.427158],[-290.352701,34.969285],[-290.407491,34.511325],[-290.461557,34.053279],[-290.514902,33.595149],[-290.567523,33.136935],[-290.619423,32.678638],[-290.670599,32.220261],[-275.486416,114.11021],[-275.666037,113.675597],[-275.844972,113.240702],[-276.023222,112.805525],[-276.200784,112.370067],[-276.37766,111.93433],[-276.553849,111.498314],[-276.729349,111.062021],[-279.468806,112.16147],[-279.645349,111.720579],[-279.821196,111.27941],[-279.996347,110.837965],[-280.170802,110.396243],[-280.34456,109.954248],[-280.517621,109.511978],[-280.689984,109.069437],[-283.496431,110.159955],[-283.669812,109.712715],[-283.842488,109.265201],[-284.014457,108.817416],[-284.18572,108.369361],[-284.356277,107.921035],[-284.526126,107.472442],[-284.695267,107.023581],[-284.863701,106.574454],[-287.740643,107.650788],[-287.910062,107.196857],[-288.078764,106.74266],[-288.24675,106.288197],[-288.414019,105.833469],[-288.580571,105.378479],[-288.746405,104.923226],[-291.692312,105.993695],[-291.524786,106.453593],[-291.356535,106.913225],[-291.18756,107.372592],[-291.01786,107.831691],[-290.847436,108.290523],[-290.676289,108.749085],[-290.504419,109.207376],[-290.331826,109.665396],[-290.158511,110.123143],[-287.228095,109.010969],[-287.055816,109.463822],[-286.882823,109.916403],[-286.709116,110.368711],[-286.534697,110.820743],[-286.359565,111.272501],[-286.18372,111.723981],[-286.007164,112.175184],[-285.829896,112.626107],[-285.651918,113.076751],[-285.473229,113.527113],[-282.618957,112.392025],[-282.441352,112.837605],[-282.263044,113.282904],[-282.084034,113.727921],[-281.904322,114.172655],[-281.723909,114.617106],[-281.542796,115.061271],[-281.360982,115.50515],[-281.178469,115.948742],[-280.995256,116.392046],[-278.213569,115.239833],[-283.833129,117.567532],[-284.018192,117.119751],[-284.202549,116.671679],[-287.102098,117.862011],[-287.287622,117.409074],[-287.472431,116.9
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
