AzizSfar/modular_shadow_lamp/output/itachi_final.scad

// Artwork is embedded. To replace it, select Artwork_source = SVG file, or rerun prepare_svg.py.
// Modular shadow lamp — millimetres. Read README.md and OPTICS.md.
// Self-contained OpenSCAD 2021.01 / MakerWorld Parametric Model Maker.
// The wall is XY at z=0; +z points into the room. Filled SVG areas transmit light.

/* [View] */
Output = "Assembly"; // [Assembly,Projection,Body,Cover,Cover base,Cover artwork,Standoff,Print layout,Stack preview,Diagnostics]
Show_rays = false;
Show_report = true;
Cover_preview = "Exploded"; // [Exploded,Fitted,Hidden]
// Wall coordinates in mm: cylinder centre = (0,0), X right, Y up.
Show_grid = false;
Grid_spacing = 25; // [5:5:100]

/* [Artwork] */
// Automatic uses a changed file path first, then embedded artwork, then the demo.
// Choose SVG file explicitly if MakerWorld keeps the uploaded filename default.svg.
Artwork_source = "Automatic"; // [Automatic,SVG file,Built-in demo,Embedded artwork]
// MakerWorld recognizes this variable as an SVG upload control.
Svg_file = "default.svg";
// Select the LONGER artwork axis. The other axis scales proportionally.
Svg_long_axis = "Y"; // [X,Y]
// Longest dimension of the complete artwork BEFORE central occlusion, in mm.
Shadow_length = 800.0; // [100:5:1500]
// Light shapes matches luminous outlines in the reference photo.
Artwork_mode = "Light shapes"; // [Light shapes,Dark silhouette]
// Small lit border around the dark silhouette field; avoids tangential, invalid cuts.
Dark_field_border = 3; // [0.5:0.5:20]
Artwork_rotation = 0; // [-180:1:180]
Shadow_x = 0; // [-1000:1:1000]
Shadow_y = 0; // [-1000:1:1000]
// Smallest IMPORTANT line or gap, as % of the artwork's longest dimension.
// This is a declared design requirement, NOT an automatic SVG measurement.
Smallest_detail_percent = 5; // [0.1:0.1:20]

/* [Cylinder] */
Housing_shape = "Cylinder"; // [Cylinder,Rectangle]
Rectangle_width = 80; // [40:1:250]
Rectangle_depth = 100; // [40:1:250]
Cylinder_diameter = 80.0; // [60:1:250]
// Total closed depth of one module, including its fitted cover.
Cylinder_height = 44.0; // [18:0.5:200]
Wall_thickness = 2; // [1.2:0.1:4]
// 0 = first module at wall; 1 = second module, etc. Recompute each module.
Module_index = 0; // [0:1:8]

/* [LED and optical quality] */
LED_position = "Automatic"; // [Automatic,Manual height]
// Height of the EMITTING CENTRE above this module's back, not package bottom.
Manual_LED_height = 24; // [0:0.1:200]
// Width of the actual emitting area, not the plastic lens or LED package.
Emitter_diameter = 0.2; // [0:0.01:5]
// Axial thickness of the emitting area. 0 assumes a planar emitter parallel to wall.
Emitter_axial_depth = 0; // [0:0.01:2]
Maximum_blur = 2; // [0.1:0.1:20]
Minimum_cut_width = 0.4; // [0.15:0.05:2]
// Emitting centre above the end of the printed pillar; measure your LED assembly.
Emitter_above_pillar = 3; // [1:0.1:10]
Pillar_diameter = 8; // [4:0.5:20]
// Continuous empty passage through the rear floor and the whole pillar, in mm.
Pillar_wire_bore = 3; // [1:0.1:6]

/* [Stencil supports] */
// Spokes interrupt light but can connect otherwise floating opaque islands.
// They do NOT guarantee connectivity for arbitrary artwork; run prepare_svg.py.
Support_bridges = true;
Support_layout = "Radial"; // [Radial,Manual XY,Radial and XY]
Bridge_count = 12; // [3:1:48]
Bridge_width = 0.9; // [0.4:0.1:2]
Bridge_rotation = 15; // [0:1:180]
// Helper mode disables the regular spokes and retains only mesh-detected repairs.
Automatic_bridges_only = true;
// Simplify narrow opaque strips in wall space using a conservative shell scale.
// 0 preserves the original geometry. This changes the shadow; inspect Projection.
Minimum_web_width = 0.6; // [0:0.1:2]

/* [Manual XY supports] */
// Segments are specified on the WALL grid. Width is the dark strip width on the wall.
// Enable Manual XY or Radial and XY in Support_layout to use these segments.
Support_1_enabled = true;
Support_1_start = [0,0];
Support_1_end = [0,200];
Support_1_width = 8; // [0.5:0.5:50]
Support_2_enabled = false;
Support_2_start = [0,0];
Support_2_end = [200,0];
Support_2_width = 8; // [0.5:0.5:50]
Support_3_enabled = false;
Support_3_start = [0,0];
Support_3_end = [0,-200];
Support_3_width = 8; // [0.5:0.5:50]
Support_4_enabled = false;
Support_4_start = [0,0];
Support_4_end = [-200,0];
Support_4_width = 8; // [0.5:0.5:50]

/* [Cover artwork and wiring] */
// White FLUSH inlay on the outward-facing circular cover; independent of shadow SVG.
Cover_artwork_source = "Automatic"; // [Automatic,None,SVG file,Embedded artwork]
Cover_svg_file = "default.svg";
Cover_svg_long_axis = "Y"; // [X,Y]
Cover_artwork_length = 65; // [5:1:240]
Cover_artwork_rotation = 0; // [-180:1:180]
Cover_artwork_depth = 0.6; // [0.2:0.1:1.2]
// Centre hole through both cover and inlay. Zero means a closed cover.
Cover_hole_diameter = 0; // [0:0.1:20]

/* [Mounting] */
// Clear gap held between the room wall and this module's back. 0 = flush to the wall.
// The gap is a closed compartment for the electronics. A standoff lifts the source,
// so the reachable image grows -- but the hidden centre widens at a similar rate.
Wall_standoff = 10.0; // [0:0.5:200]
// Separate ring prints the gap as its own part that plugs into the rear socket.
// Extended body grows the body backwards instead, as one piece with no extra joint.
Standoff_mode = "Separate ring"; // [Separate ring,Extended body]
// Back plate of the compartment. It carries the keyholes and the cable route.
Standoff_back = 3; // [1.5:0.1:8]

/* [Joints and cover] */
Joint_depth = 2.5; // [1.5:0.1:4]
Joint_clearance = 0.2; // [0.1:0.05:0.4]
Cover_plate = 2; // [1.5:0.1:3]
// Radial pilot holes in female collars for optional retaining screws.
Retaining_screws = true;
Screw_pilot_diameter = 2.1; // [1.5:0.1:3]

/* [Quality] */
Cylinder_facets = 180; // [72:12:360]

/* [Hidden] */
// Compatibility with older saved presets; Artwork_source overrides this control.
Use_svg = false;
$fn = Cylinder_facets;
eps = 0.02;
// prepare_svg.py replaces this block with normalized, embedded SVG geometry.
Embedded_artwork = true;
Embedded_radius_factor = 0.5000706693625946;
// Extra bridge angles added by the helper after checking the actual exported mesh.
Embedded_bridge_angles = [];
// [angle, local top Z] vertical ribs added only as far as a floating island.
Embedded_bridge_segments = [[254.68018,30.18982],[267.20591,0.45],[265.42345,25.61084],[85.67525,21.30191],[116.15299,25.56195],[100.82625,21.50445],[145.541,32.719550000000005],[211.08272,30.62539]];
Embedded_removed_islands = [[[290.89298239481747,105.70322470395874],[291.0644316660633,105.68848799398485],[291.0644502680775,105.68848744854631],[291.0685125974609,105.68901760982746],[291.6138099779818,105.76174074627625],[291.61386691025535,105.7617614162746],[291.8212797120531,105.84716844426093],[291.8226395788807,105.84811553254092],[291.9922743351621,105.96926495093501],[292.03155960516233,106.11696907532802]],[[-96.82590734422448,-37.448558637750246],[-96.80667259622213,-37.498214996136646],[-96.80666470434761,-37.498211274880184],[-96.78957726263216,-37.48781086974433],[-96.78955042700261,-37.48779259587127],[-96.6660074728386,-37.3867325137853],[-96.66601214833798,-37.38673197845156]],[[298.38141229664274,83.99987065696101],[298.3814264689674,83.99986773944671],[299.54647291642664,84.32784196416193],[299.5465074110796,84.32785899981728],[299.0112194340561,84.30176638725335],[299.0111045989544,84.3017306020395],[298.5628973742805,84.13211640568638],[298.55950423839323,84.13083030467385],[298.38264282309115,84.00078345288381]],[[-296.94304457440234,87.14408862451414],[-296.4598490338776,87.00228650043879],[-296.4601203523719,87.00614944786798],[-296.50871633046984,87.52437074230583],[-296.508803749714,87.52439080202045],[-296.5120724651832,87.52158132190245]]];
Embedded_surface_repair = true;
Embedded_surface_signature = [80.0,80,100,44.0,10.0,0,800.0,0,0,0,0.6,24,3,8,2,2.5,2,"Automatic","Light shapes",3,"Cylinder"];
// BEGIN EMBEDDED PRINT LIGHT
module embedded_print_light() { polygon(points=[[92.263776,11.850815],[92.244971,11.99631],[92.225937,12.141775],[92.206673,12.28721],[92.187181,12.432614],[92.469949,12.470749],[92.754458,12.509119],[93.040723,12.547725],[93.060396,12.400975],[93.079838,12.254193],[93.099049,12.107381],[93.118028,11.960539],[92.831525,11.92374],[92.54678,11.887165],[92.147507,12.723329],[92.127326,12.86864],[92.106917,13.013918],[92.086278,13.159164],[92.06541,13.304377],[92.044313,13.449558],[92.022987,13.594704],[92.001432,13.739817],[91.979649,13.884896],[92.261781,13.927486],[92.545649,13.970337],[92.83127,14.013453],[92.853255,13.867031],[92.875009,13.720575],[92.896533,13.574084],[92.917825,13.42756],[92.938886,13.281002],[92.959716,13.134411],[92.980315,12.987788],[93.000682,12.841132],[92.71454,12.801623],[92.430154,12.762356],[91.333146,17.643768],[91.305207,17.787788],[91.27704,17.931764],[91.248646,18.075695],[91.220025,18.219581],[91.191178,18.363422],[91.162103,18.507217],[91.132802,18.650966],[91.103274,18.794669],[91.382718,18.852318],[91.663882,18.910322],[91.946781,18.968685],[91.976582,18.823651],[92.006155,18.678571],[92.035498,18.533445],[92.064613,18.388272],[92.093499,18.243054],[92.122156,18.09779],[92.150583,17.952481],[92.178781,17.807128],[91.895168,17.75234],[91.613295,17.697887],[287.952705,31.459356],[287.902732,31.913448],[287.852044,32.367461],[287.800639,32.821393],[287.748518,33.275244],[287.695682,33.729012],[287.64213,34.182696],[287.587862,34.636295],[287.53288,35.089808],[287.477182,35.543234],[287.420769,35.996571],[287.363641,36.449819],[287.305799,36.902976],[287.247241,37.356041],[287.18797,37.809014],[287.127984,38.261892],[287.067284,38.714675],[287.00587,39.167362],[289.765114,39.543913],[289.702388,40.000853],[289.638943,40.457694],[289.574776,40.914435],[289.50989,41.371073],[289.444284,41.827609],[289.377957,42.284041],[289.310911,42.740368],[289.243145,43.196588],[289.17466,43.652701],[289.105455,44.108705],[289.035532,44.564599],[288.964889,45.020383],[288.893528,45.476055],[288.821448,45.931613],[288.74865,46.387058],[288.675134,46.842387],[288.6009,47.297599],[288.525947,47.752694],[288.450278,48.20767],[291.250327,48.675633],[291.173199,49.134904],[291.095346,49.594053],[291.016769,50.053079],[290.937468,50.511981],[290.857443,50.970757],[290.776695,51.429406],[290.695224,51.887927],[290.61303,52.346319],[290.530113,52.804581],[290.446473,53.262712],[290.362111,53.72071],[290.277027,54.178574],[290.191221,54.636304],[290.104693,55.093898],[290.017443,55.551354],[289.929472,56.008673],[289.84078,56.465852],[289.751367,56.922891],[289.661234,57.379788],[292.500601,57.942246],[292.408856,58.403478],[292.316384,58.864565],[292.223185,59.325505],[292.129259,59.786298],[292.034606,60.246941],[291.939228,60.707436],[291.843122,61.167779],[291.746292,61.62797],[291.648735,62.088007],[291.550453,62.54789],[291.451446,63.007618],[291.351714,63.467189],[291.251257,63.926602],[291.150076,64.385856],[291.048171,64.84495],[290.945542,65.303882],[290.842189,65.762653],[290.738113,66.221259],[290.633313,66.679701],[290.527791,67.137977],[290.421546,67.596086],[293.296548,68.265248],[293.188522,68.727722],[293.079766,69.190025],[292.970282,69.652157],[292.860069,70.114115],[292.749127,70.575898],[292.637458,71.037506],[292.52506,71.498938],[292.411935,71.960191],[292.298083,72.421266],[292.183503,72.88216],[292.068197,73.342873],[291.952165,73.803404],[291.835406,74.263751],[291.717921,74.723914],[291.599711,75.18389],[291.480776,75.64368],[294.395113,76.399995],[294.274257,76.864191],[294.152668,77.328197],[294.030347,77.79201],[293.907296,78.25563],[293.783513,78.719055],[293.658999,79.182284],[293.533755,79.645317],[293.407781,80.108151],[293.281078,80.570786],[293.153644,81.03322],[293.025482,81.495453],[292.896591,81.957484],[292.766971,82.41931],[295.723731,83.251693],[298.740824,84.10106],[301.820114,84.967937],[301.685736,85.443833],[301.550607,85.919517],[298.474066,85.042931],[298.339573,85.51355],[298.204338,85.983957],[298.068362,86.454149],[297.931644,86.924126],[297.794185,87.393887],[297.655986,87.863431],[297.517046,88.332756],[297.377366,88.801862],[297.236946,89.270746],[297.095787,89.739409],[294.095308,88.833098],[293.954844,89.296806],[293.813648,89.760293],[293.671721,90.223556],[293.529064,90.686595],[293.385677,91.149408],[293.24156,91.611994],[293.096713,92.074353],[292.951138,92.536482],[292.804834,92.998381],[292.657802,93.460049],[292.510041,93.921485],[295.494347,94.87971],[298.540174,95.857689],[298.388625,96.328398],[298.236334,96.798868],[298.083301,97.269098],[297.929527,97.739085],[294.88993,96.741912],[294.736991,97.206864],[294.583319,97.671574],[291.608215,96.685153],[288.692603,95.718457],[288.541286,96.173636],[288.389251,96.628576],[288.236499,97.083276],[288.08303,97.537734],[287.928845,97.99195],[287.773943,98.445922],[290.680277,99.440163],[293.645915,100.454692],[293.487122,100.917677],[293.327599,101.380411],[293.167347,101.842893],[293.006366,102.305122],[292.844655,102.767096],[295.863171,103.826375],[298.944561,104.907718],[298.778739,105.379054],[295.699058,104.292853],[295.534209,104.759071],[295.368626,105.225029],[295.202307,105.690725],[295.035255,106.156159],[294.867469,106.621328],[294.698949,107.086232],[291.692312,105.993695],[288.746405,104.923226],[285.859406,103.874163],[285.695231,104.324864],[285.530344,104.775305],[285.364747,105.225486],[285.198441,105.675405],[285.031425,106.125061],[282.209783,105.074486],[282.043718,105.51943],[281.876952,105.964111],[281.709485,106.408528],[281.541318,106.852681],[281.37245,107.296568],[281.202882,107.740188],[281.032615,108.18354],[280.861649,108.626624],[278.108538,107.561825],[277.938556,108.000297],[277.767883,108.438501],[277.596519,108.876435],[277.424464,109.314098],[277.251719,109.75149],[277.078285,110.188608],[276.904161,110.625452],[276.729349,111.062021],[274.043077,109.983918],[273.86928,110.415976],[273.694802,110.847759],[273.519643,111.279266],[273.343804,111.710497],[273.167285,112.141449],[272.990087,112.572123],[272.812209,113.002517],[275.486416,114.11021],[278.213569,115.239833],[280.995256,116.392046],[283.833129,117.567532],[286.728909,118.767003],[289.684386,119.991201],[292.701425,121.2409],[295.781969,122.516903],[298.928046,123.820051],[302.141769,125.151218],[305.425343,126.511319],[308.78107,127.901307],[308.9824,127.414168],[309.182961,126.926712],[309.382753,126.438941],[309.581776,125.950855],[309.780029,125.462455],[309.977511,124.973744],[310.174222,124.484722],[310.370161,123.99539],[310.565329,123.50575],[310.759724,123.015802],[310.953347,122.525549],[311.146195,122.034991],[311.33827,121.544129],[311.529571,121.052965],[311.720097,120.5615],[311.909847,120.069735],[312.098821,119.577671],[312.28702,119.08531],[312.474441,118.592653],[312.661086,118.099701],[312.846952,117.606455],[313.032041,117.112916],[313.216351,116.619087],[309.812422,115.35171],[309.993958,114.86296],[310.174724,114.373925],[310.354718,113.884604],[310.53394,113.395001],[310.712389,112.905116],[310.890066,112.41495],[311.066969,111.924504],[311.243099,111.43378],[311.418455,110.942778],[311.593036,110.451501],[311.766842,109.959949],[311.939872,109.468123],[312.112127,108.976026],[312.283605,108.483657],[312.454307,107.991018],[312.624231,107.498111],[312.793378,107.004936],[312.961747,106.511495],[309.597151,105.366409],[309.762939,104.878011],[309.927958,104.389352],[310.092205,103.900434],[306.793918,102.7953],[306.955655,102.311326],[307.116629,101.827098],[307.276839,101.342616],[307.436285,100.857883],[307.594966,100.372898],[307.752882,99.887664],[307.910032,99.402181],[308.066417,98.916452],[308.222035,98.430476],[308.376887,97.944255],[308.530972,97.457791],[308.684289,96.971084],[308.836839,96.484136],[308.98862,95.996949],[309.139633,95.509522],[309.289877,95.021858],[309.439352,94.533957],[309.588057,94.045822],[309.735992,93.557452],[309.883157,93.06885],[310.029551,92.580016],[310.175173,92.090952],[310.320025,91.601659],[310.464104,91.112138],[310.607411,90.622391],[310.749946,90.132418],[310.891708,89.642221],[311.032696,89.151801],[311.172911,88.661159],[311.312352,88.170296],[311.451019,87.679215],[311.588911,87.187915],[311.726027,86.696399],[311.862369,86.204666],[311.997935,85.71272],[312.132725,85.22056],[312.266738,84.728188],[308.980278,83.836464],[309.112113,83.349066],[309.243178,82.86146],[309.373475,82.373648],[309.503002,81.885632],[309.631759,81.397411],[309.759746,80.908989],[309.886963,80.420365],[310.013409,79.931541],[310.139084,79.442518],[310.263987,78.953297],[310.388119,78.46388],[310.511479,77.974269],[310.634066,77.484463],[310.755881,76.994464],[310.876922,76.504274],[310.997191,76.013893],[311.116686,75.523324],[311.235407,75.032567],[311.353354,74.541623],[311.470527,74.050493],[311.586925,73.55918],[311.702548,73.067683],[311.817396,72.576005],[311.931468,72.084146],[312.044764,71.592108],[312.157284,71.099892],[312.269028,70.607499],[312.379995,70.114931],[312.490185,69.622188],[312.599598,69.129272],[312.708233,68.636184],[312.816091,68.142925],[312.92317,67.649496],[309.664101,66.944933],[309.769295,66.456477],[309.873719,65.967856],[309.977372,65.479071],[310.080254,64.990123],[310.182364,64.501013],[310.283703,64.011743],[310.384271,63.522314],[310.484066,63.032726],[310.583089,62.542982],[310.681339,62.053082],[310.778817,61.563029],[310.875522,61.072821],[310.971454,60.582462],[311.066612,60.091953],[311.160996,59.601294],[311.254607,59.110486],[311.347443,58.619532],[311.439505,58.128431],[311.530792,57.637187],[311.621305,57.145799],[311.711042,56.654268],[311.800004,56.162597],[311.88819,55.670786],[311.975601,55.178837],[308.759893,54.610077],[308.845634,54.123063],[308.930608,53.635914],[309.014813,53.148631],[309.09825,52.661217],[309.180918,52.173671],[309.262816,51.685996],[309.343946,51.198192],[309.424306,50.710261],[309.503897,50.222203],[309.582717,49.734021],[309.660768,49.245715],[309.738049,48.757286],[309.814559,48.268737],[309.890298,47.780067],[309.965267,47.291278],[310.039465,46.802372],[310.112891,46.313349],[310.185547,45.824211],[310.257431,45.334959],[310.328543,44.845595],[310.398883,44.356118],[310.468451,43.866532],[310.537247,43.376836],[310.605271,42.887033],[307.436351,42.449482],[307.502916,41.96457],[307.568716,41.479554],[307.633751,40.994434],[307.698021,40.509213],[307.761525,40.023891],[307.824264,39.538469],[307.886238,39.052949],[307.947445,38.567332],[308.007887,38.081619],[308.067563,37.595811],[308.126472,37.109909],[308.184615,36.623916],[308.241992,36.137831],[308.298601,35.651656],[308.354444,35.165393],[308.40952,34.679042],[308.463829,34.192605],[308.517371,33.706083],[308.570145,33.219477],[308.622152,32.732789],[308.673391,32.246019],[308.723863,31.759168],[308.773566,31.272239],[305.65515,30.956409],[302.599091,30.646895],[299.603539,30.343509],[299.555311,30.815977],[299.506339,31.288369],[299.456621,31.760683],[299.406159,32.232917],[299.354952,32.705072],[296.420563,32.384485],[293.543144,32.070122],[290.721052,31.761803],[292.973508,111.720433],[292.796949,112.182344],[292.619662,112.643976],[292.441647,113.105327],[292.262904,113.566398],[292.083435,114.027185],[291.903239,114.48769],[288.925124,113.31964],[289.103482,112.863834],[289.28112,112.407747],[289.458039,111.951381],[289.634238,111.494737],[289.809717,111.037815],[289.984475,110.580616],[256.638692,128.326143],[256.435989,128.730729],[256.232649,129.134995],[256.028671,129.53894],[255.824056,129.942563],[255.618805,130.345862],[255.412918,130.748838],[257.845048,131.993874],[260.323943,133.262849],[262.850964,134.55646],[265.427527,135.875433],[268.055103,137.220519],[270.735222,138.592503],[273.469475,139.992199],[276.259521,141.420456],[279.107084,142.878156],[282.013961,144.366221],[284.982025,145.885607],[288.013228,147.437315],[287.780346,147.891359],[287.546748,148.345034],[287.312435,148.798341],[287.077407,149.251278],[286.841666,149.703843],[286.60521,150.156036],[286.368042,150.607855],[286.130162,151.0593],[285.89157,151.51037],[285.652267,151.961062],[285.412253,152.411376],[285.171529,152.861312],[284.930096,153.310867],[284.687955,153.76004],[284.445105,154.208832],[284.201548,154.657239],[283.957284,155.105263],[283.712314,155.5529],[283.466638,156.00015],[283.220257,156.447013],[282.973171,156.893486],[282.725382,157.339569],[282.47689,157.785261],[282.227695,158.23056],[281.977798,158.675466],[281.727199,159.119977],[281.4759,159.564092],[284.501998,161.279537],[284.247289,161.728026],[283.991874,162.176112],[283.735752,162.623795],[283.478925,163.071074],[283.221392,163.517947],[282.963155,163.964413],[282.704214,164.410472],[282.44457,164.856121],[282.184224,165.301361],[281.923175,165.746189],[281.661426,166.190605],[281.398975,166.634608],[281.135825,167.078196],[280.871976,167.521369],[280.607428,167.964125],[280.342182,168.406463],[280.076239,168.848382],[279.809599,169.289882],[279.542264,169.73096],[279.274233,170.171616],[279.005507,170.611849],[278.736087,171.051658],[278.465974,171.491041],[278.195169,171.929997],[277.923671,172.368526],[277.651483,172.806626],[277.378603,173.244297],[277.105034,173.681536],[276.830776,174.118344],[279.839278,176.010603],[279.561343,176.451719],[279.282713,176.892397],[279.003388,177.332635],[278.723369,177.772432],[278.442656,178.211787],[278.161252,178.650698],[277.879155,179.089165],[277.596367,179.527187],[280.646336,181.499664],[283.76407,183.515965],[286.951853,185.577569],[290.212072,187.686018],[293.547224,189.842929],[293.846261,189.379738],[294.144567,188.916077],[294.442142,188.451945],[294.738984,187.987345],[295.035093,187.522277],[295.330468,187.056743],[295.625109,186.590743],[295.919014,186.12428],[296.212184,185.657353],[296.504616,185.189965],[296.796311,184.722116],[297.087268,184.253807],[297.377486,183.785041],[297.666965,183.315817],[297.955703,182.846137],[298.243699,182.376002],[298.530954,181.905414],[298.817467,181.434374],[299.103236,180.962882],[299.388262,180.49094],[299.672542,180.018549],[296.267796,177.973258],[296.54811,177.505792],[296.827687,177.037884],[297.106525,176.569536],[297.384624,176.100748],[297.661983,175.631523],[297.938602,175.16186],[298.21448,174.691762],[298.489616,174.22123],[298.76401,173.750264],[299.037661,173.278866],[299.310568,172.807037],[299.58273,172.334778],[299.854147,171.862091],[300.124819,171.388976],[300.394744,170.915434],[300.663922,170.441468],[300.932352,169.967078],[301.200033,169.492265],[301.466966,169.01703],[301.733148,168.541375],[301.99858,168.065301],[302.263261,167.588809],[302.52719,167.1119],[302.790367,166.634575],[303.05279,166.156836],[303.31446,165.678683],[303.575376,165.200119],[303.835536,164.721144],[304.09494,164.241758],[304.353588,163.761965],[300.934505,161.922276],[301.189499,161.44747],[301.443744,160.972262],[301.697239,160.496653],[301.949984,160.020646],[302.201977,159.54424],[302.453219,159.067438],[302.703709,158.59024],[302.953446,158.112647],[303.202429,157.634662],[303.450659,157.156284],[303.698133,156.677515],[303.944852,156.198357],[304.190815,155.71881],[304.436022,155.238875],[304.680471,154.758555],[304.924162,154.27785],[305.167095,153.796761],[305.409269,153.315289],[305.650684,152.833436],[305.891338,152.351203],[306.131231,151.868591],[306.370363,151.385602],[306.608733,150.902236],[306.84634,150.418494],[307.083184,149.934378],[307.319264,149.44989],[307.55458,148.965029],[307.789131,148.479799],[308.022916,147.994198],[308.255935,147.50823],[308.488188,147.021895],[305.061156,145.388611],[305.290069,144.907317],[305.518223,144.425663],[305.745618,143.943649],[305.972252,143.461277],[306.198125,142.978549],[306.423236,142.495465],[306.647585,142.012026],[306.871171,141.528234],[307.093994,141.044091],[307.316054,140.559596],[307.537349,140.074752],[307.757879,139.589559],[307.977643,139.104019],[308.196642,138.618134],[308.414874,138.131903],[308.632338,137.645329],[308.849036,137.158412],[309.064965,136.671155],[309.280125,136.183557],[309.494516,135.695621],[309.708137,135.207347],[309.920988,134.718737],[310.133068,134.229792],[310.344377,133.740513],[310.554913,133.250901],[310.764678,132.760958],[310.973669,132.270684],[311.181887,131.780082],[311.389331,131.289152],[311.596,130.797895],[311.801895,130.306313],[308.376108,128.874629],[308.578973,128.388128],[308.78107,127.901307],[305.425343,126.511319],[302.141769,125.151218],[298.928046,123.820051],[295.781969,122.516903],[292.701425,121.2409],[289.684386,119.991201],[286.728909,118.767003],[283.833129,117.567532],[280.995256,116.392046],[278.213569,115.239833],[275.486416,114.11021],[272.812209,113.002517],[272.633653,113.43263],[272.454419,113.86246],[272.274507,114.292008],[272.093918,114.721271],[271.912653,115.150249],[271.73071,115.57894],[271.548093,116.007344],[271.364799,116.435459],[271.180831,116.863285],[273.839046,118.008822],[276.549891,119.17704],[276.361592,119.61304],[276.172606,120.048742],[273.46546,118.871979],[273.277646,119.303115],[273.089153,119.733954],[272.899981,120.164495],[272.710129,120.594737],[272.5196,121.02468],[272.328392,121.454321],[272.136507,121.88366],[271.943946,122.312696],[269.304127,121.12538],[269.112764,121.54995],[268.920733,121.974218],[268.728032,122.398182],[268.534663,122.821842],[268.340627,123.245196],[268.145922,123.668244],[267.950551,124.090984],[267.754514,124.513416],[267.55781,124.935538],[264.985538,123.734421],[264.790066,124.152177],[264.593936,124.569624],[264.397148,124.986761],[264.199702,125.403588],[264.001599,125.820102],[263.802839,126.236304],[263.603423,126.652191],[263.403351,127.067764],[263.202625,127.48302],[260.696318,126.269083],[260.496854,126.680071],[260.296743,127.090744],[260.095984,127.501101],[259.894578,127.911141],[259.692525,128.320863],[259.489827,128.730265],[259.286483,129.139347],[259.082495,129.548109],[260.026969,251.951857],[259.629292,252.361634],[259.230968,252.770782],[258.832,253.179302],[261.949852,256.229063],[265.143734,259.353193],[268.416462,262.554446],[268.830204,262.130799],[269.243277,261.7065],[269.65568,261.28155],[266.367843,258.095816],[263.159216,254.986832],[93.110012,93.110012],[92.963052,93.25674],[92.815861,93.403237],[92.668439,93.549501],[93.071317,93.956209],[93.477713,94.36647],[93.887674,94.780328],[94.037036,94.63214],[94.186164,94.483716],[94.335057,94.335057],[93.923143,93.923143],[93.51481,93.51481],[92.730686,95.100649],[92.580587,95.246777],[92.430257,95.392667],[92.279698,95.538321],[92.684405,95.957319],[93.092678,96.380008],[93.504563,96.806438],[93.65712,96.658851],[93.809445,96.511024],[93.961536,96.362957],[93.547638,95.938481],[93.13737,95.517727],[80.196872,187.723527],[79.900713,187.849772],[79.604355,187.975551],[79.307799,188.100861],[79.843604,189.371674],[80.386698,190.659776],[80.937231,191.96552],[81.23988,191.837635],[81.542327,191.709273],[81.844571,191.580434],[81.287867,190.277308],[80.738684,188.991791],[212.409875,287.940917],[211.955498,288.275552],[211.500594,288.609469],[211.045164,288.942668],[210.589209,289.275149],[210.13273,289.606911],[209.675728,289.937952],[209.218205,290.268272],[208.760162,290.597869],[208.301599,290.926745],[207.842518,291.254896],[207.38292,291.582323],[206.922807,291.909025],[206.462179,292.235001],[206.001037,292.56025],[205.539383,292.884771],[205.077217,293.208564],[204.614542,293.531627],[204.151357,293.853961],[203.687665,294.175563],[203.223467,294.496434],[205.642329,298.001671],[208.119466,301.591355],[210.657009,305.268575],[213.257195,309.036572],[215.922373,312.898751],[216.415578,312.55783],[216.908245,312.216131],[217.400373,311.873656],[217.89196,311.530405],[218.383005,311.186379],[218.873506,310.841579],[219.363464,310.496007],[219.852875,310.149661],[220.34174,309.802545],[220.830057,309.454658],[221.317825,309.106001],[221.805042,308.756575],[222.291707,308.406382],[222.77782,308.055421],[223.263378,307.703694],[223.748381,307.351202],[224.232828,306.997945],[224.716717,306.643925],[221.942989,302.858951],[222.420353,302.508547],[222.897164,302.157391],[220.17944,298.473269],[217.527191,294.877904],[214.938079,291.368127],[198.954313,313.0215],[198.460399,313.334882],[197.96599,313.647485],[197.471089,313.959308],[199.908518,317.834577],[202.406871,321.806709],[204.968461,325.87938],[205.482151,325.555718],[205.995331,325.231246],[206.507998,324.905966],[203.927169,320.84546],[201.410051,316.885194],[8.281703,111.523104],[8.105809,111.536026],[7.929895,111.548671],[7.753962,111.561039],[7.578008,111.573129],[7.402037,111.584942],[7.226046,111.596477],[7.050038,111.607734],[6.874012,111.618714],[6.899376,112.030567],[6.722684,112.041308],[6.747581,112.456251],[6.570217,112.466753],[6.392838,112.476975],[6.416601,112.89508],[6.238546,112.905059],[6.261823,113.326322],[6.285274,113.750739],[6.308901,114.178347],[6.332707,114.609183],[6.356693,115.043282],[6.53812,115.033114],[6.719531,115.02266],[6.745079,115.459981],[6.927163,115.4492],[7.10923,115.438132],[7.136363,115.878708],[7.319107,115.867309],[7.347148,116.311218],[7.530574,116.299486],[7.713981,116.287465],[7.743648,116.734696],[7.927741,116.722339],[8.111814,116.709691],[8.295868,116.696752],[8.4799,116.683524],[8.663912,116.670005],[8.630719,116.223021],[8.597779,115.779449],[8.56509,115.33925],[8.532648,114.902386],[8.500452,114.468818],[8.468497,114.03851],[8.436782,113.611426],[8.405303,113.187528],[8.374059,112.766782],[8.343045,112.349152],[8.312261,111.934604],[19.424616,114.01398],[19.24478,114.044473],[19.064896,114.074682],[18.884965,114.104608],[18.704987,114.134249],[18.524962,114.163607],[18.595663,114.599319],[18.666907,115.03837],[18.738698,115.480798],[18.811044,115.926642],[18.88395,116.375942],[18.957424,116.828738],[19.031472,117.285071],[19.1061,117.744984],[19.181316,118.208517],[19.257127,118.675715],[19.069939,118.705938],[18.882704,118.735865],[18.695422,118.765498],[18.508093,118.794835],[18.320718,118.823876],[18.393414,119.295369],[18.46669,119.770619],[18.540552,120.249671],[18.730176,120.220281],[18.919752,120.190592],[19.109282,120.160604],[19.298764,120.130317],[19.488198,120.099732],[19.677583,120.068847],[19.86692,120.037664],[20.056207,120.006183],[20.245444,119.974403],[20.434631,119.942325],[20.623767,119.909948],[20.812852,119.877273],[21.001885,119.8443],[21.190866,119.811029],[21.106446,119.333724],[21.294621,119.300289],[21.482744,119.266557],[21.670813,119.232528],[21.858828,119.198203],[22.046789,119.163581],[22.234695,119.128662],[22.146467,118.65596],[22.333573,118.620885],[22.245303,118.152058],[22.157729,117.686922],[22.070841,117.225433],[21.984633,116.76755],[21.800451,116.802077],[21.715629,116.347623],[21.631465,115.896691],[21.448657,115.930662],[21.265796,115.964345],[21.183694,115.516634],[21.001486,115.549899],[20.819225,115.582877],[20.739156,115.138355],[20.557545,115.17092],[20.478786,114.729679],[20.29782,114.761834],[20.116803,114.793703],[20.040026,114.355586],[19.85965,114.387049],[19.679225,114.418227],[19.498752,114.449121],[72.380352,368.433602],[71.799203,368.547295],[71.217877,368.660072],[70.636373,368.771931],[70.054693,368.882873],[69.472839,368.992898],[68.890813,369.102005],[68.308615,369.210194],[67.726247,369.317465],[67.143711,369.423817],[66.561007,369.52925],[65.978138,369.633764],[65.395105,369.737359],[64.81191,369.840034],[65.621895,374.462102],[66.452383,379.201162],[67.30416,384.06171],[68.178057,389.04848],[69.074947,394.166452],[69.696502,394.057024],[70.317884,393.946615],[70.939092,393.835227],[71.560123,393.722859],[72.180976,393.609511],[72.801649,393.495185],[73.422141,393.37988],[74.042451,393.263596],[74.662577,393.146334],[75.282517,393.028095],[75.902269,392.908878],[76.521833,392.788683],[77.141206,392.667512],[76.139582,387.569002],[75.163636,382.601196],[74.212391,377.759131],[73.284924,373.038094],[55.459844,371.357564],[54.874105,371.444568],[54.28823,371.530648],[53.70222,371.615804],[53.116077,371.700036],[52.529801,371.783343],[51.943394,371.865726],[51.356859,371.947184],[50.770196,372.027716],[50.183406,372.107323],[49.596492,372.186005],[50.216323,376.837392],[50.851843,381.606512],[51.503655,386.497892],[52.172393,391.516294],[52.858726,396.666731],[53.484245,396.582874],[54.109631,396.498031],[54.734883,396.412201],[55.359998,396.325385],[55.984976,396.237584],[56.609814,396.148797],[57.234511,396.059025],[57.859066,395.968268],[58.483478,395.876525],[59.107743,395.783798],[58.340271,390.644826],[57.592474,385.637594],[56.863604,380.757102],[56.152952,375.998598],[143.953223,357.053091],[143.389934,357.279676],[142.826288,357.50537
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
