AzizSfar/modular_shadow_lamp/output/demo_assembly.png

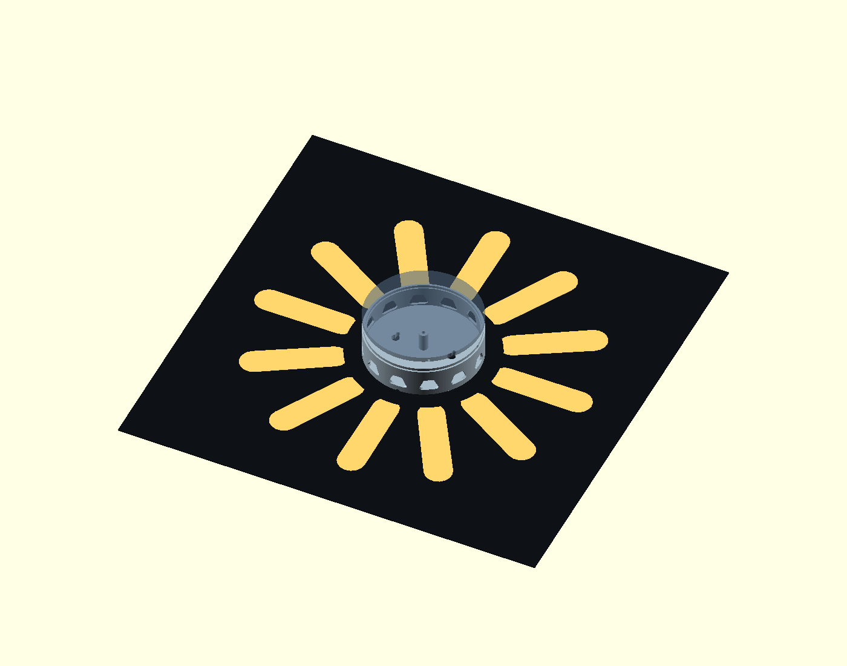
output/demo_assembly.png
