AzizSfar/modular_shadow_lamp/output/features_assembly.png

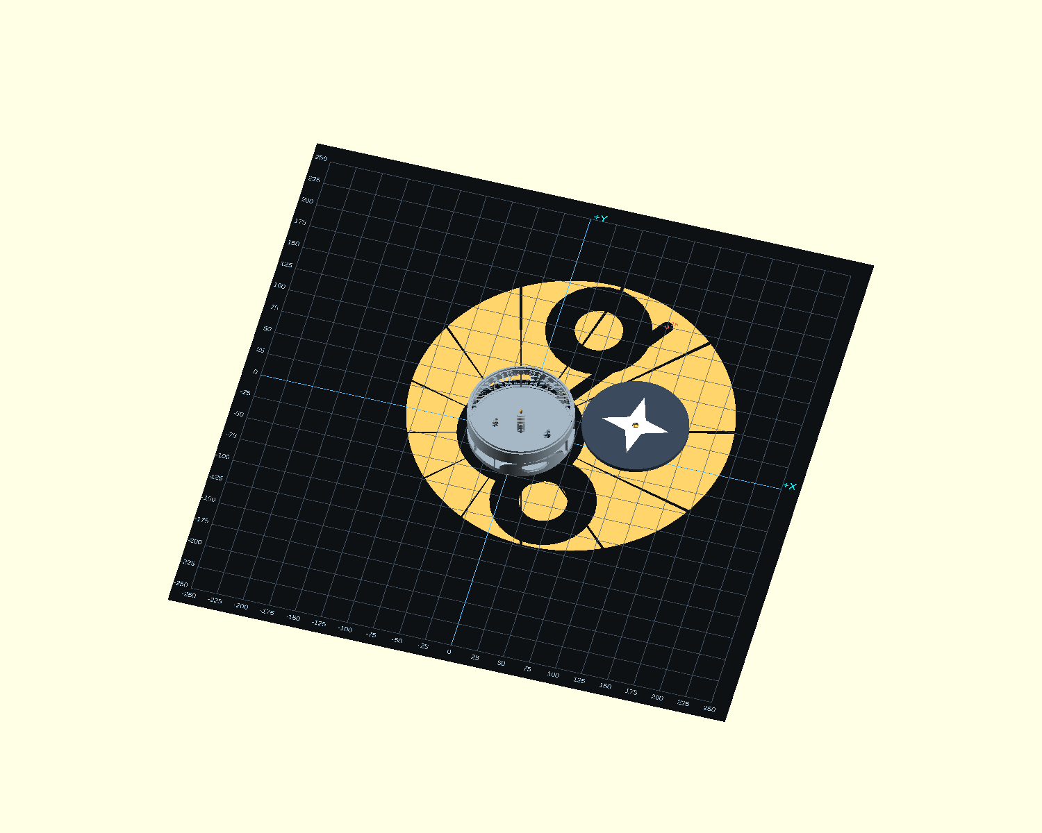
output/features_assembly.png
