AzizSfar/modular_shadow_lamp/output/itachi_compact_projection/repaired.png

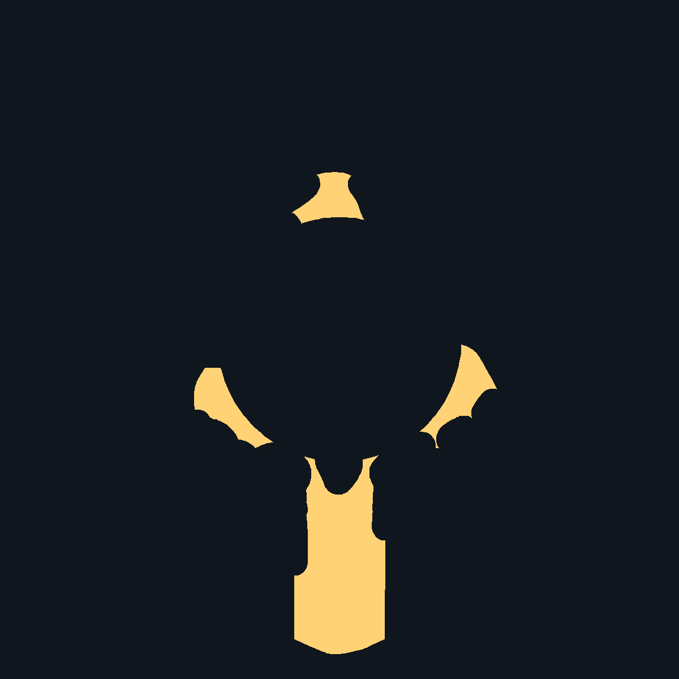
output/itachi_compact_projection/repaired.png
