AzizSfar/modular_shadow_lamp/output/itachi_compact_projection/unrepaired.png

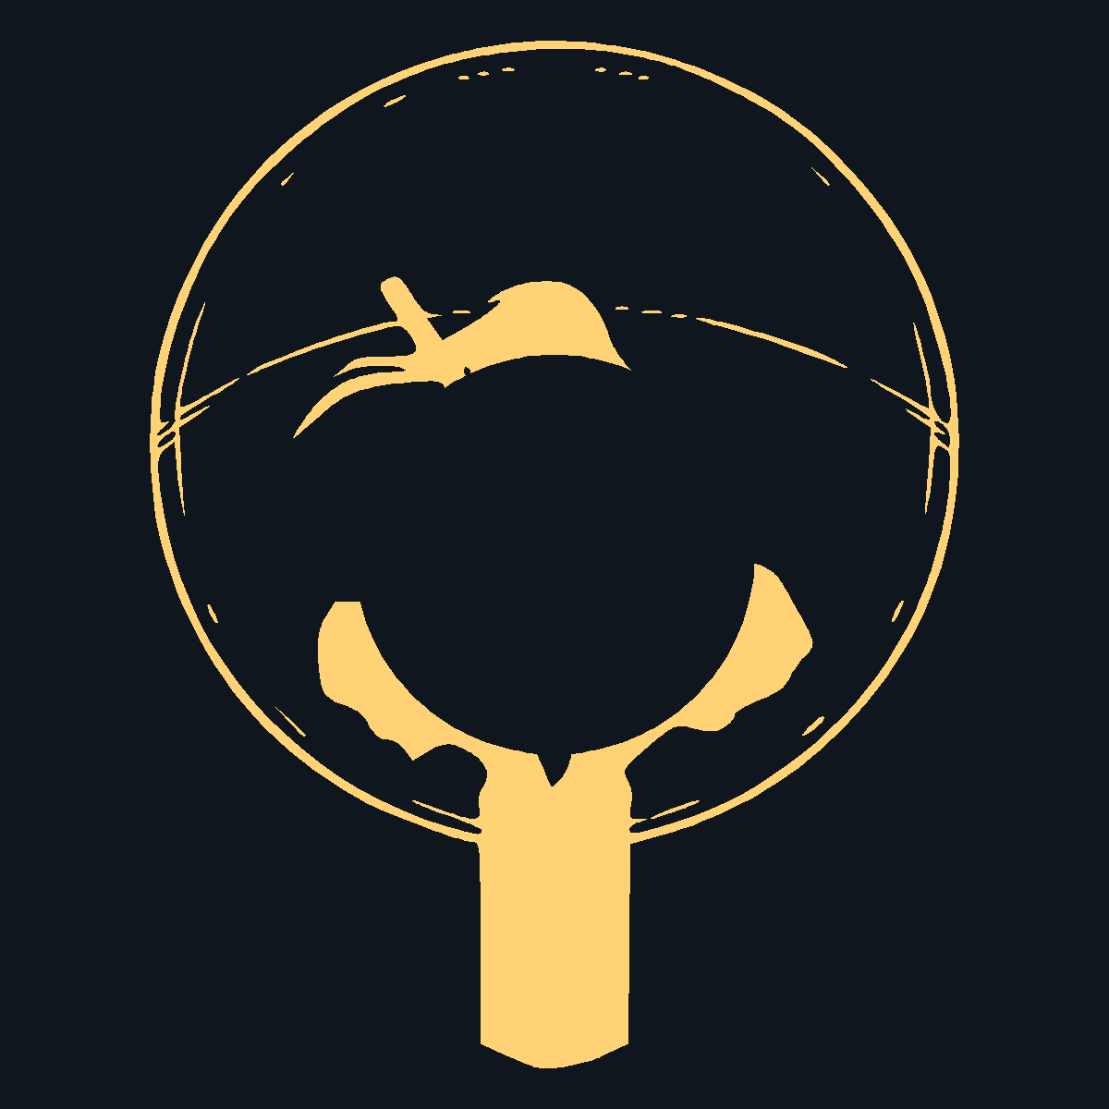
output/itachi_compact_projection/unrepaired.png
